sbarisic/MagMouse/hardware/bench/WURTH_ENQUIRY.md

> SUPERSEDED for soldered-wire Rev-A. Historical enquiry record only; no reply
> or additional message is required for this revision. Do not send a follow-up.

# FFC compatibility enquiry

Submitted with the user's authorization through Würth's
[contact form](https://www.we-online.com/en/support/contact) on 2026-09-11.
The site confirmed receipt: "Thank you for your inquiry."
Reply is pending at the user-provided email. Contact details are not stored here.

Requested one 150 mm, 30-conductor, 0.5 mm, same-side-contact FFC for two
Hirose FH12-30S-0.5SH(55) connectors. Requested confirmation of conductor span
14.5 +/-0.05 mm, width 15.5 +/-0.07 mm, end thickness 0.30 +/-0.05 mm,
exposed contacts >=3.5 mm, and stiffener >=0.188 mm. Explained the drawing
tolerance mismatch and inadequate length of trial part 687630050002.

Requested an exact alternative part/drawing, orientation, MOQ, stock, unit
price and delivery options to Croatia 43000, preferably stocked distribution
for one or a few pieces. Explicitly stated that this is an enquiry, not an order.

Do not close cable qualification until the reply or another manufacturer's
conforming drawing identifies an available cable. Measure cable continuity
against the connector pin map before applying power even after qualification.
