sbarisic/MagMouse/hardware/quotes/2026-09-11/Encoder/evidence/drill-report.txt

Drill report for Encoder.kicad_pcb
Created on 2026-09-11T18:30:18

Copper Layer Stackup:
    =============================================================
    L1 :  F.Cu                      front
    L2 :  B.Cu                      back

Drill file 'Encoder-PTH.drl' contains
    plated through holes:
    =============================================================
    T1  0.300mm  0.0118"  (17 holes))

    Total plated holes count 17

Drill file 'Encoder-NPTH.drl' contains
    unplated through holes:
    =============================================================

    Total unplated holes count 0
