sbarisic/MagMouse/hardware/quotes/2026-09-11/Main/evidence/drill-report.txt

Drill report for Main.kicad_pcb
Created on 2026-09-11T18:30:00

Copper Layer Stackup:
    =============================================================
    L1 :  F.Cu                      front
    L2 :  In1.Cu                    in1
    L3 :  In2.Cu                    in2
    L4 :  B.Cu                      back

Drill file 'Main-PTH.drl' contains
    plated through holes:
    =============================================================
    T1  0.200mm  0.0079"  (554 holes))
    T2  0.300mm  0.0118"  (321 holes))
    T3  0.600mm  0.0236"  (4 holes)  (with 4 slots)
    T4  0.700mm  0.0276"  (16 holes))

    Total plated holes count 895

Drill file 'Main-NPTH.drl' contains
    unplated through holes:
    =============================================================
    T1  0.650mm  0.0256"  (2 holes))

    Total unplated holes count 2
