sbarisic/MagMouse/hardware/quotes/2026-09-11/Wheel/evidence/drill-report.txt

Drill report for Wheel.kicad_pcb
Created on 2026-09-11T18:30:11

Copper Layer Stackup:
    =============================================================
    L1 :  F.Cu                      front
    L2 :  In1.Cu                    in1
    L3 :  In2.Cu                    in2
    L4 :  B.Cu                      back

Drill file 'Wheel-PTH.drl' contains
    plated through holes:
    =============================================================
    T1  0.200mm  0.0079"  (56 holes))
    T2  0.300mm  0.0118"  (140 holes))
    T3  1.000mm  0.0394"  (3 holes))

    Total plated holes count 199

Drill file 'Wheel-NPTH.drl' contains
    unplated through holes:
    =============================================================

    Total unplated holes count 0
