sbarisic/MagMouse/hardware/bench/copper-images/index.html

# MagMouse: copper layer review

Click a preview for the full-resolution image (up to 6000 pixels), or open the SVG for unrestricted zoom.

All layers are viewed from the TOP, without mirroring, so positions line up between layers. B.Cu is a through-board view, not an underside photograph. Plots include saved filled zones, tracks, pads, actual drill openings and Edge.Cuts; they exclude solder mask and silkscreen.

Panel note: this is the current working geometry, updated after the JLC submission. The Main-right and Encoder-top replacement tabs now connect across their full width to both board and frame. Images are for manual review, not replacement fabrication files.

Gallery generated 2026-09-13T02:50:26.760Z. Source hashes below identify the board geometry; refresh older open image tabs.

All router corner close-ups

Detail views: U16 pad and via entries · Main B.Cu repair · Wheel MISO simplification · U6 coil via entry · repaired pictured corner · both relocated tabs.

Source identities: SHA-256 manifest. No source board was edited or refilled by this export.

## Main — F.Cu

Source 8409ba354f256351

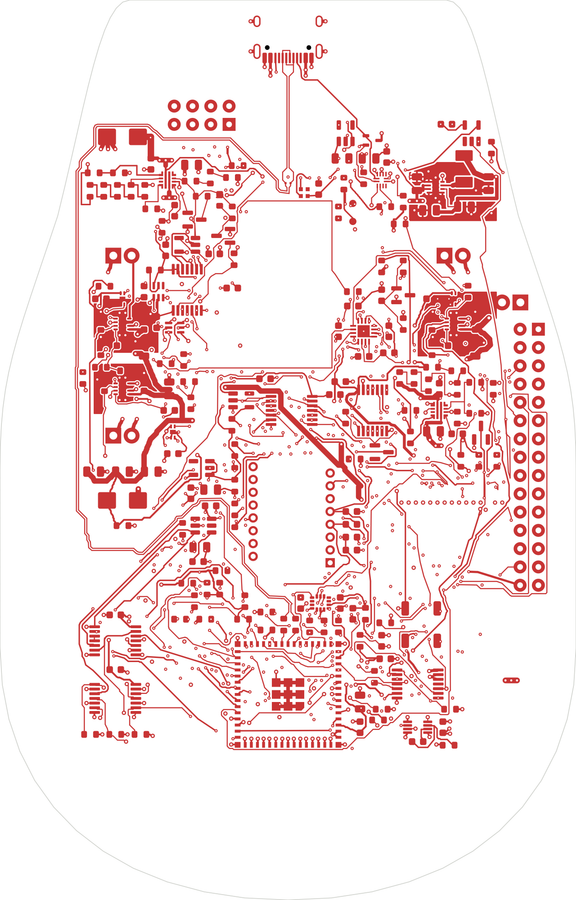
[picture p1: hardware/bench/copper-images/Main-F.Cu-preview.png]
Main F.Cu copper


Full-resolution PNG · Vector SVG

## Main — In1.Cu

Source 8409ba354f256351

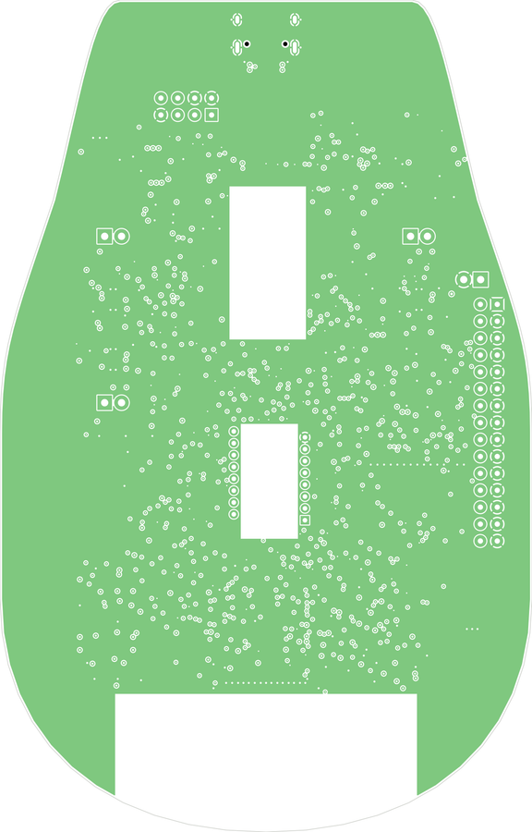
[picture p2: hardware/bench/copper-images/Main-In1.Cu-preview.png]
Main In1.Cu copper


Full-resolution PNG · Vector SVG

## Main — In2.Cu

Source 8409ba354f256351

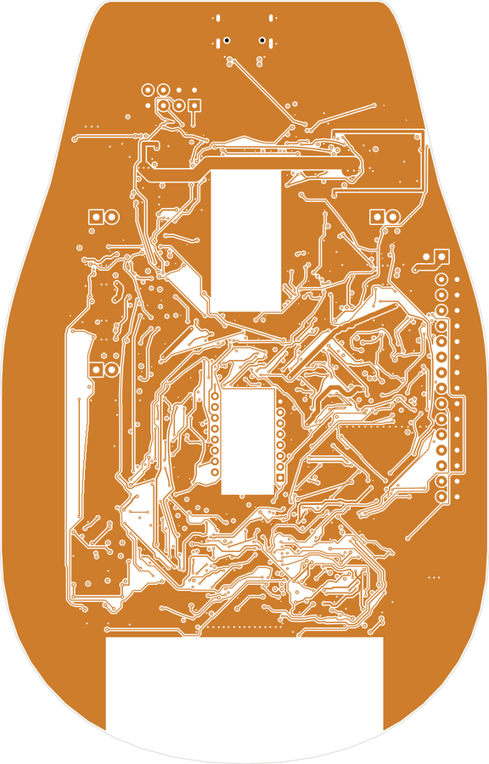
[picture p3: hardware/bench/copper-images/Main-In2.Cu-preview.png]
Main In2.Cu copper


Full-resolution PNG · Vector SVG

## Main — B.Cu

Source 8409ba354f256351

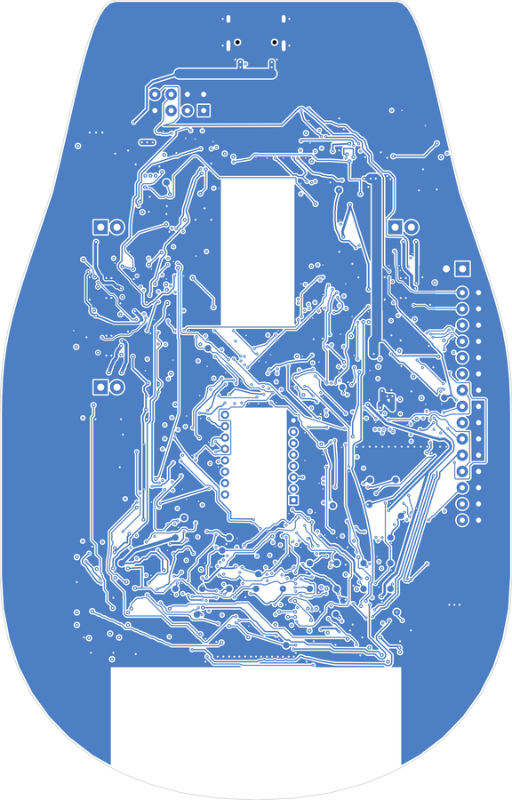
[picture p4: hardware/bench/copper-images/Main-B.Cu-preview.png]
Main B.Cu copper


Full-resolution PNG · Vector SVG

## Wheel — F.Cu

Source e2eaaa13c60e927e

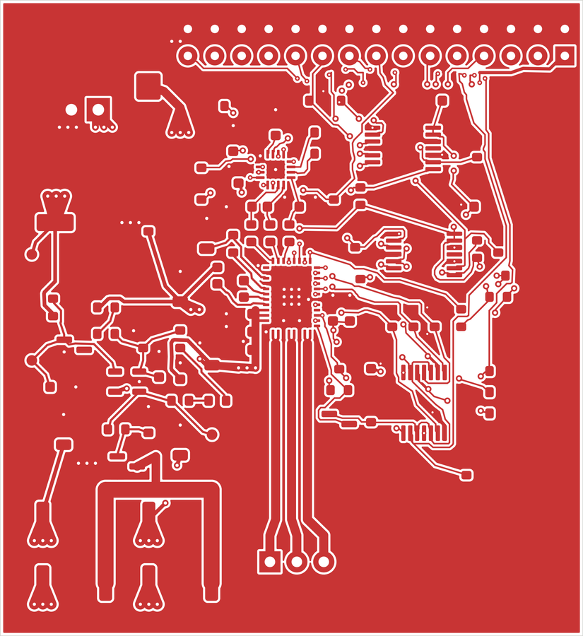
[picture p5: hardware/bench/copper-images/Wheel-F.Cu-preview.png]
Wheel F.Cu copper


Full-resolution PNG · Vector SVG

## Wheel — In1.Cu

Source e2eaaa13c60e927e

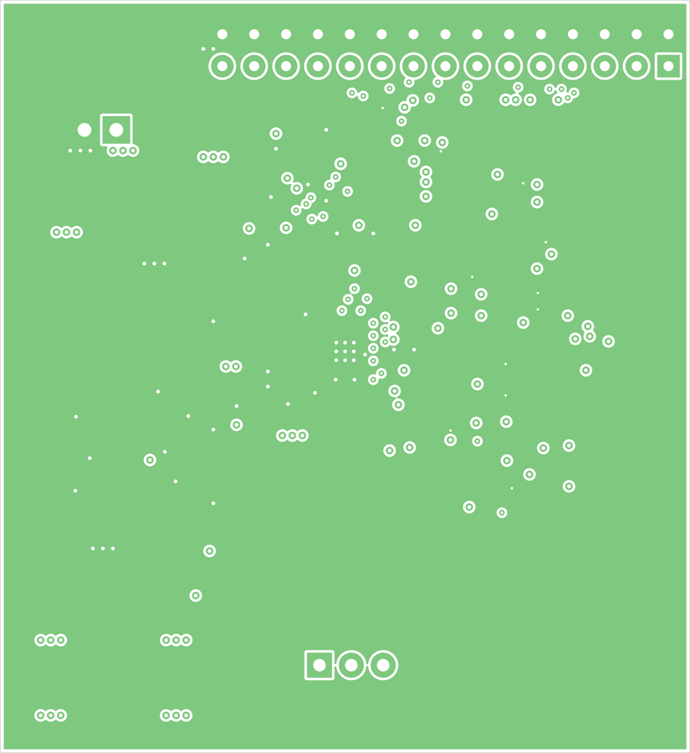
[picture p6: hardware/bench/copper-images/Wheel-In1.Cu-preview.png]
Wheel In1.Cu copper


Full-resolution PNG · Vector SVG

## Wheel — In2.Cu

Source e2eaaa13c60e927e

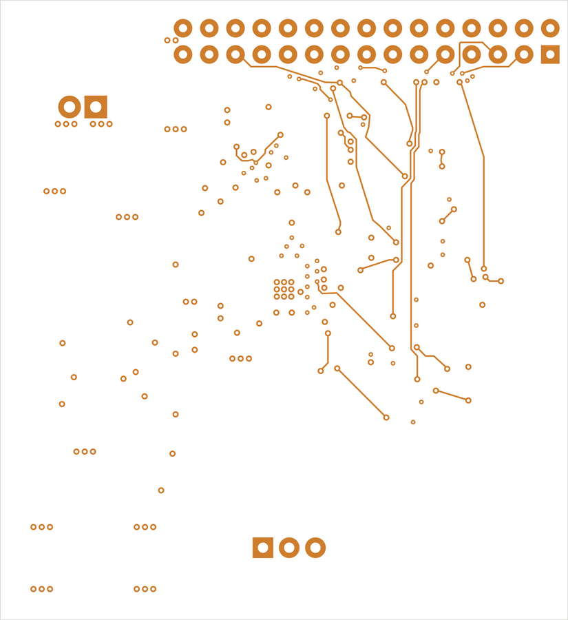
[picture p7: hardware/bench/copper-images/Wheel-In2.Cu-preview.png]
Wheel In2.Cu copper


Full-resolution PNG · Vector SVG

## Wheel — B.Cu

Source e2eaaa13c60e927e

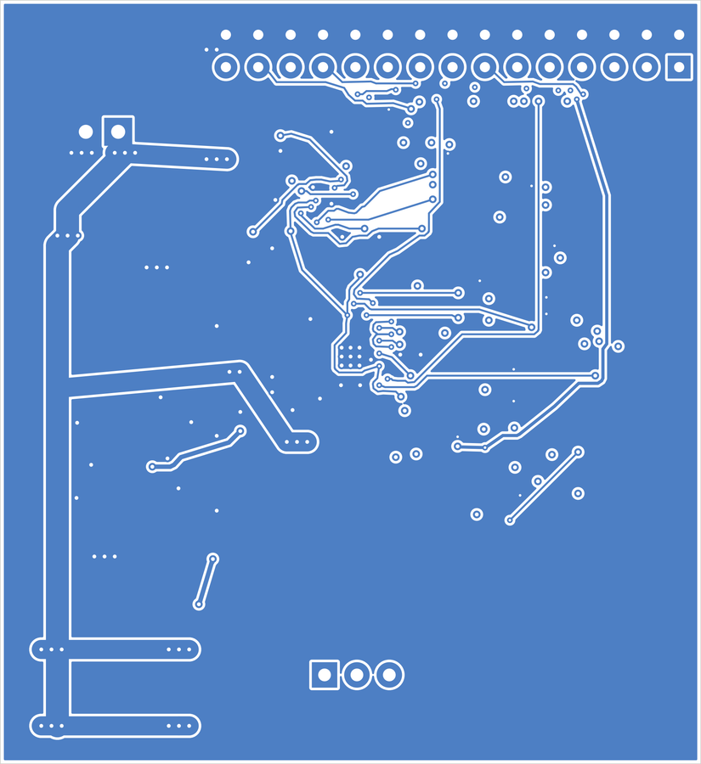
[picture p8: hardware/bench/copper-images/Wheel-B.Cu-preview.png]
Wheel B.Cu copper


Full-resolution PNG · Vector SVG

## Encoder — F.Cu

Source 32b3366d89d79553

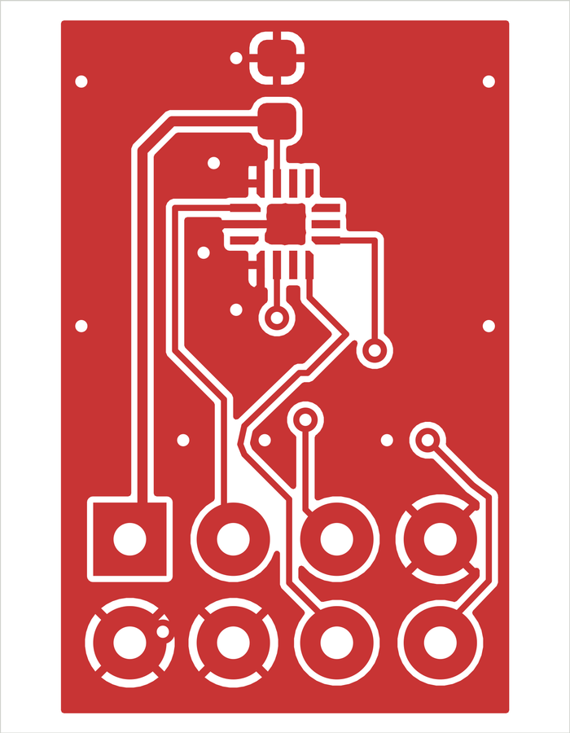
[picture p9: hardware/bench/copper-images/Encoder-F.Cu-preview.png]
Encoder F.Cu copper


Full-resolution PNG · Vector SVG

## Encoder — In1.Cu

Source 32b3366d89d79553

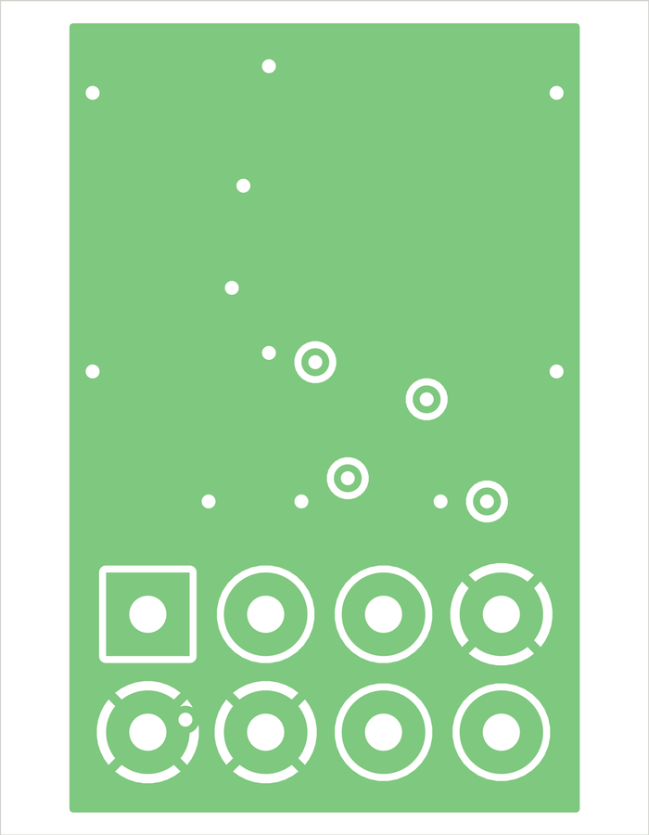
[picture p10: hardware/bench/copper-images/Encoder-In1.Cu-preview.png]
Encoder In1.Cu copper


Full-resolution PNG · Vector SVG

## Encoder — In2.Cu

Source 32b3366d89d79553

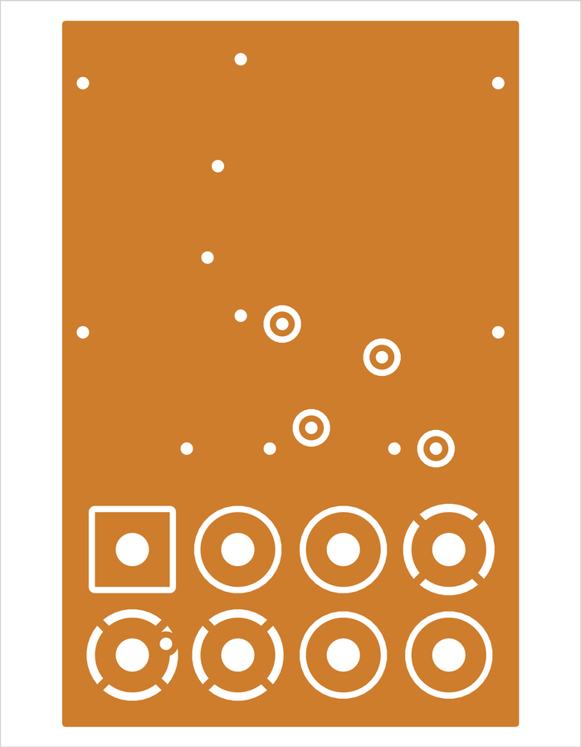
[picture p11: hardware/bench/copper-images/Encoder-In2.Cu-preview.png]
Encoder In2.Cu copper


Full-resolution PNG · Vector SVG

## Encoder — B.Cu

Source 32b3366d89d79553

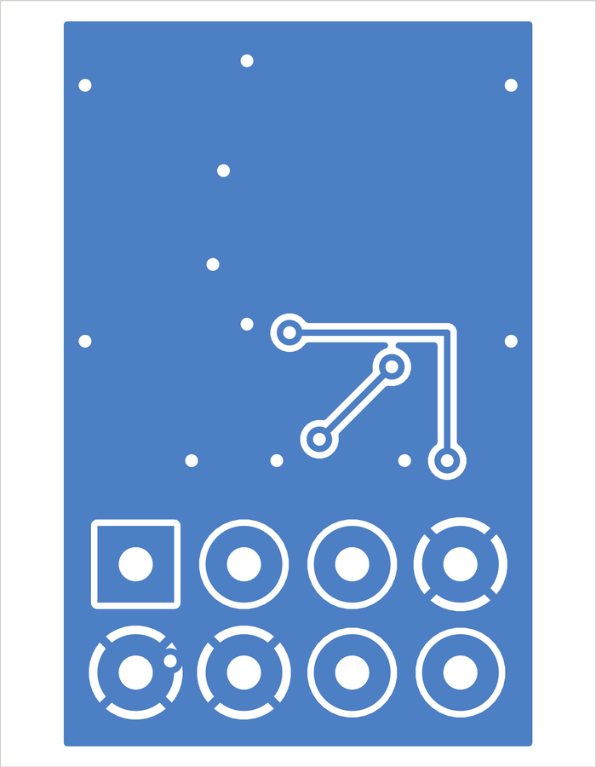
[picture p12: hardware/bench/copper-images/Encoder-B.Cu-preview.png]
Encoder B.Cu copper


Full-resolution PNG · Vector SVG

## Panel — F.Cu

Source 6ce26abbf629e559

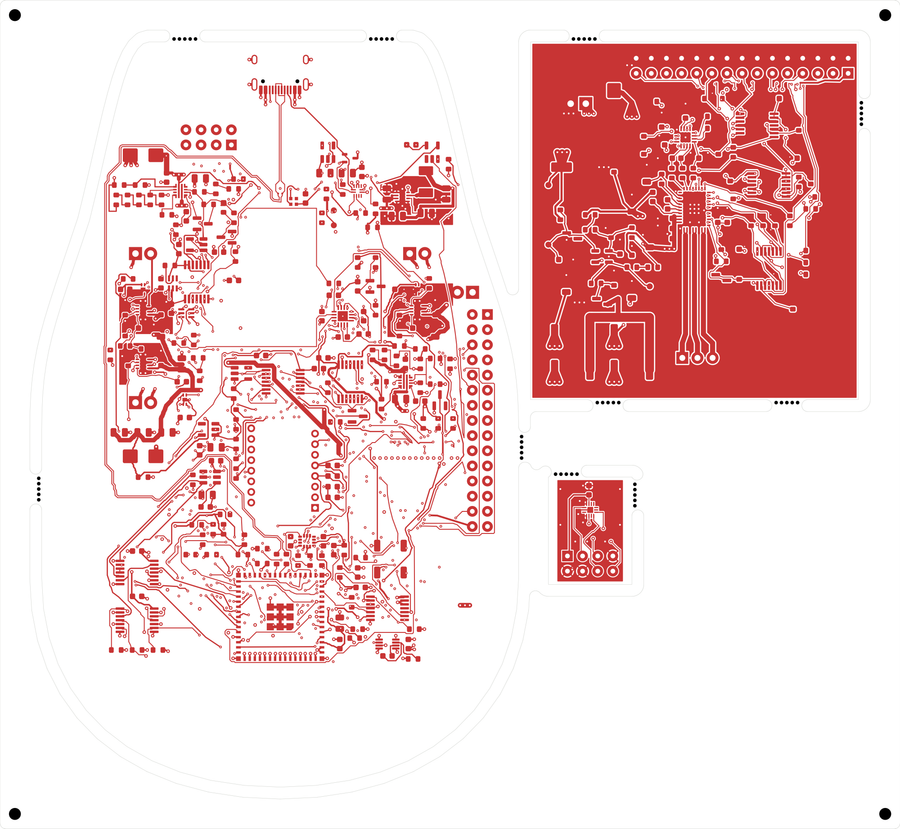
[picture p13: hardware/bench/copper-images/Panel-F.Cu-preview.png]
Panel F.Cu copper


Full-resolution PNG · Vector SVG

## Panel — In1.Cu

Source 6ce26abbf629e559

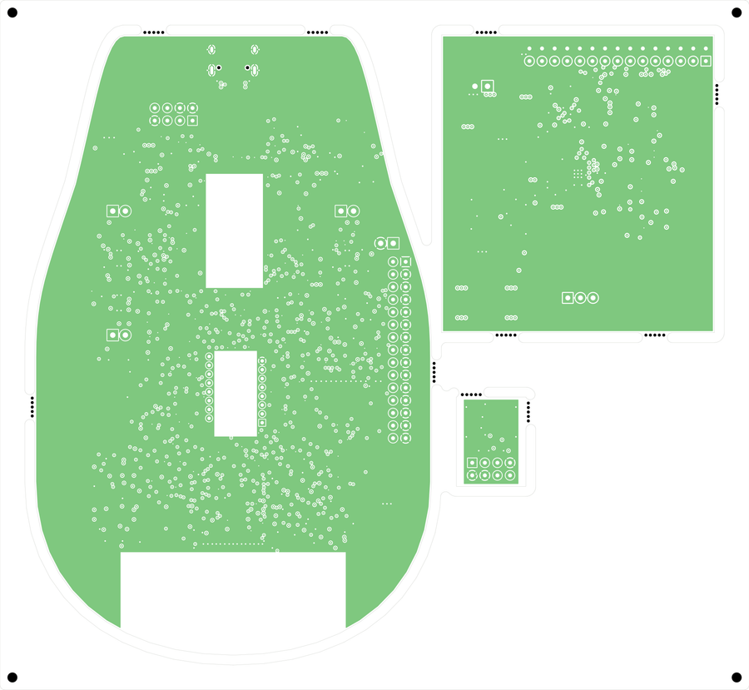
[picture p14: hardware/bench/copper-images/Panel-In1.Cu-preview.png]
Panel In1.Cu copper


Full-resolution PNG · Vector SVG

## Panel — In2.Cu

Source 6ce26abbf629e559

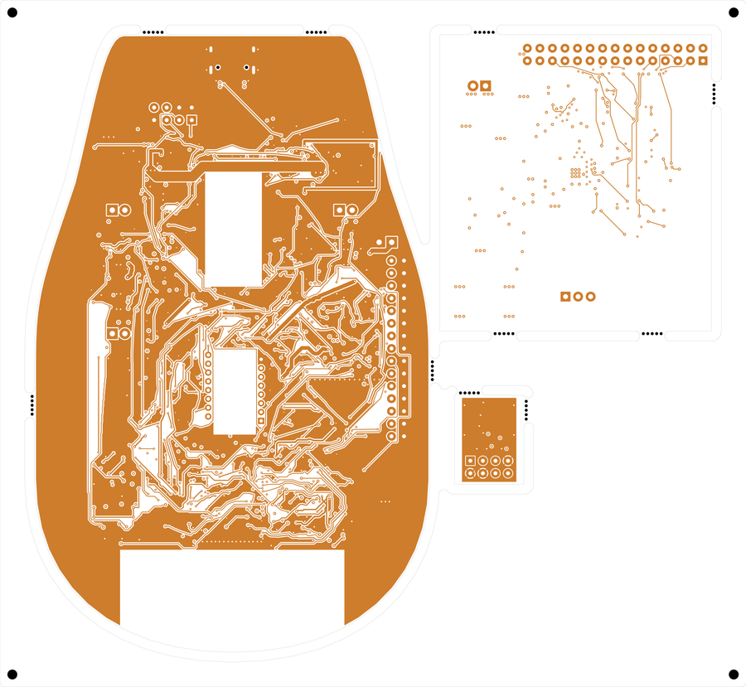
[picture p15: hardware/bench/copper-images/Panel-In2.Cu-preview.png]
Panel In2.Cu copper


Full-resolution PNG · Vector SVG

## Panel — B.Cu

Source 6ce26abbf629e559

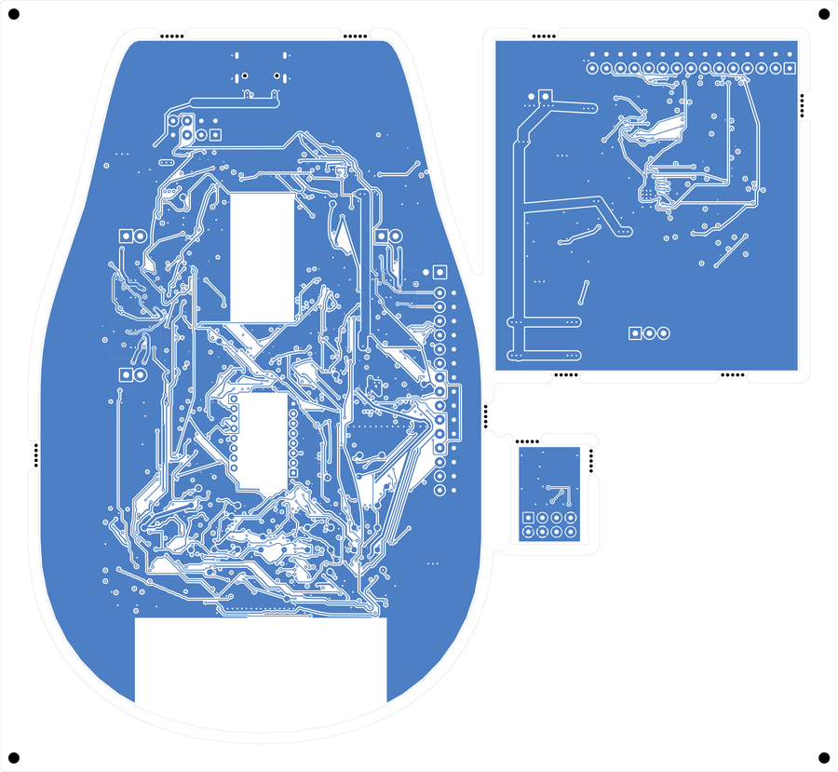
[picture p16: hardware/bench/copper-images/Panel-B.Cu-preview.png]
Panel B.Cu copper


Full-resolution PNG · Vector SVG
