sbarisic/MagMouse/hardware/bench/router-images/index.html

# 2 mm cutter / 1 mm radius

Panel SHA256: 6ce26abbf629e5592f26f47651ea0b0219b7810e1122b6fbaca9ea3bea7f399e

All 40 retained corner patches; 4 × 4 mm views. Pale green is retained material; white is routed away. Factory CAM approval remains pending.

## corner-01, opening 1

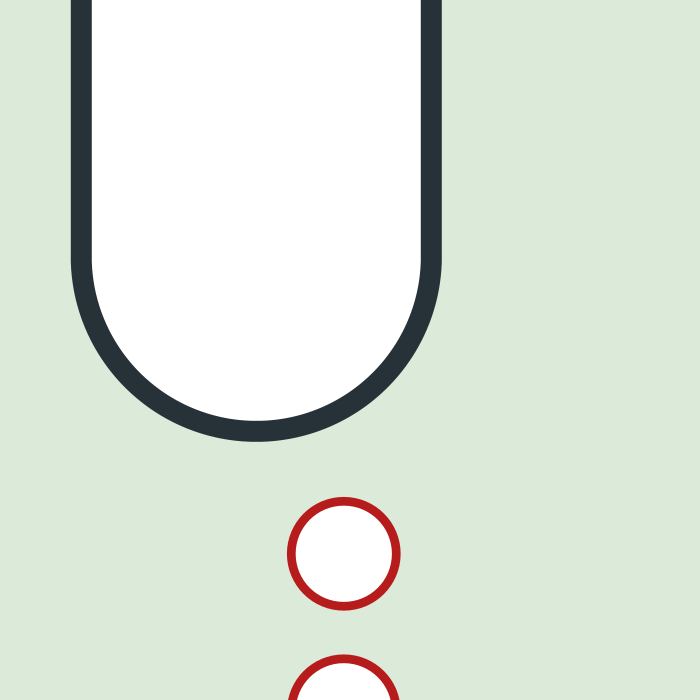
[picture p17: hardware/bench/router-images/corner-01.png]


## corner-02, opening 1

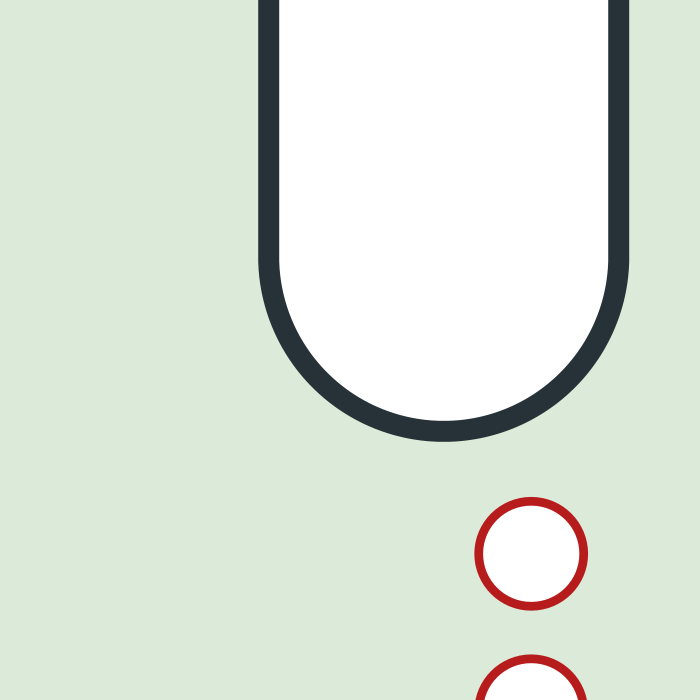
[picture p18: hardware/bench/router-images/corner-02.png]


## corner-03, opening 1

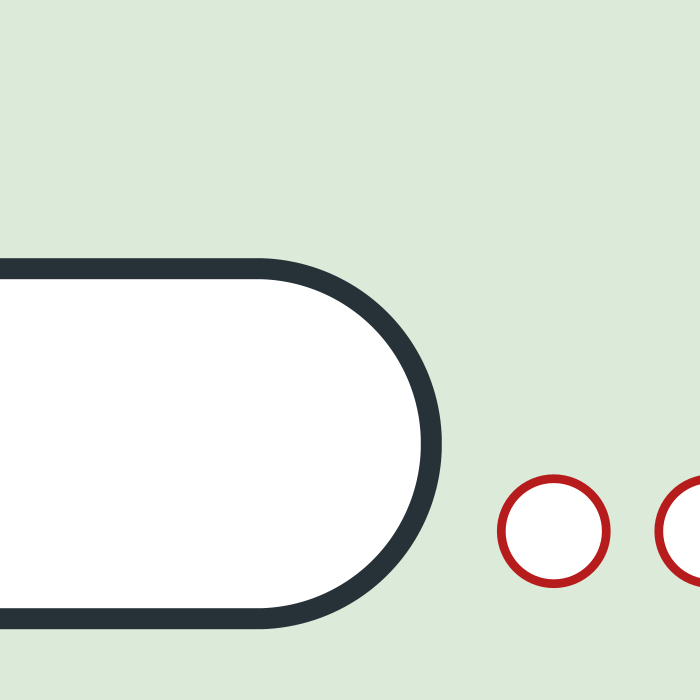
[picture p19: hardware/bench/router-images/corner-03.png]


## corner-04, opening 1

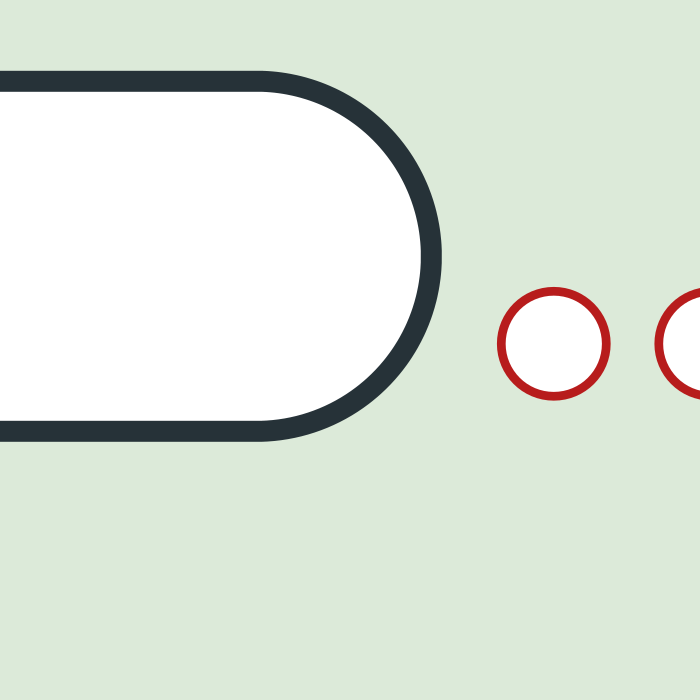
[picture p20: hardware/bench/router-images/corner-04.png]


## corner-05, opening 2

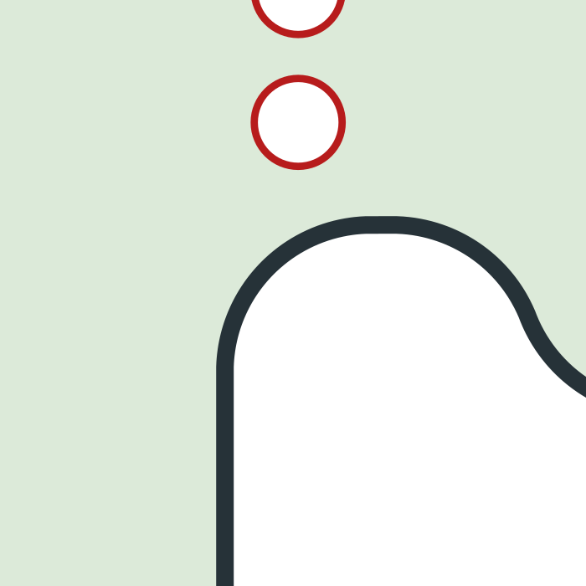
[picture p21: hardware/bench/router-images/corner-05.png]


## corner-06, opening 2

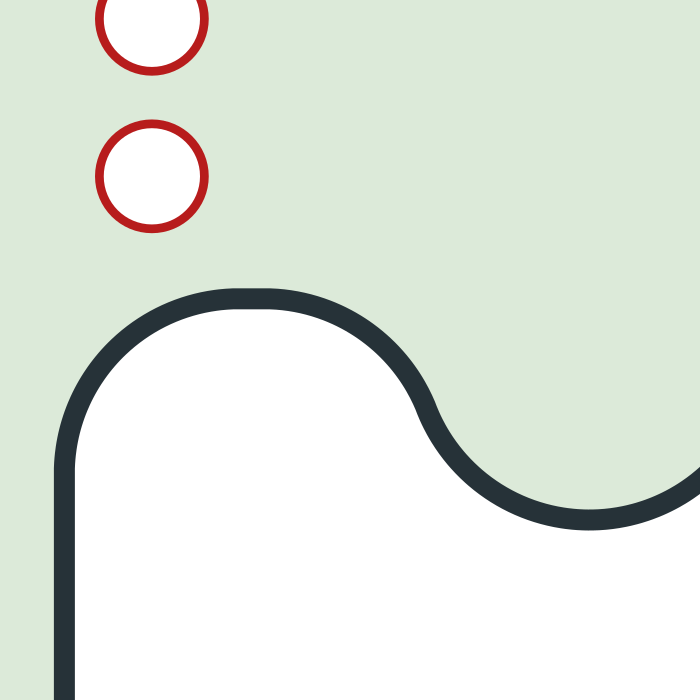
[picture p22: hardware/bench/router-images/corner-06.png]


## corner-07, opening 2

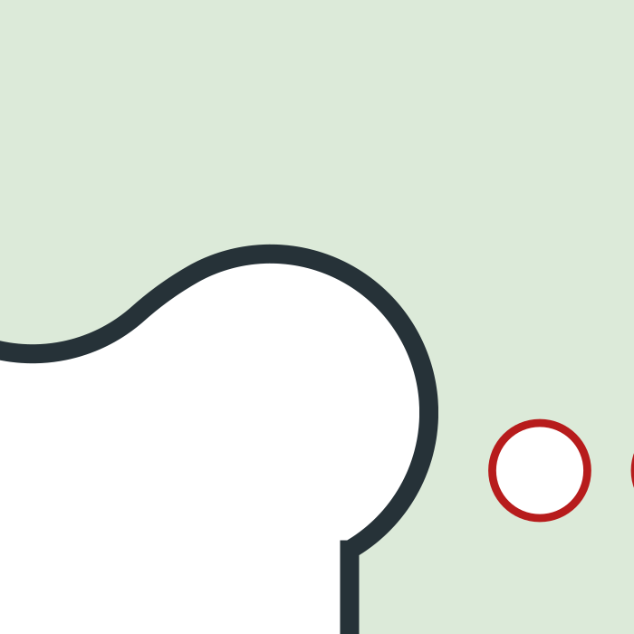
[picture p23: hardware/bench/router-images/corner-07.png]


## corner-08, opening 2

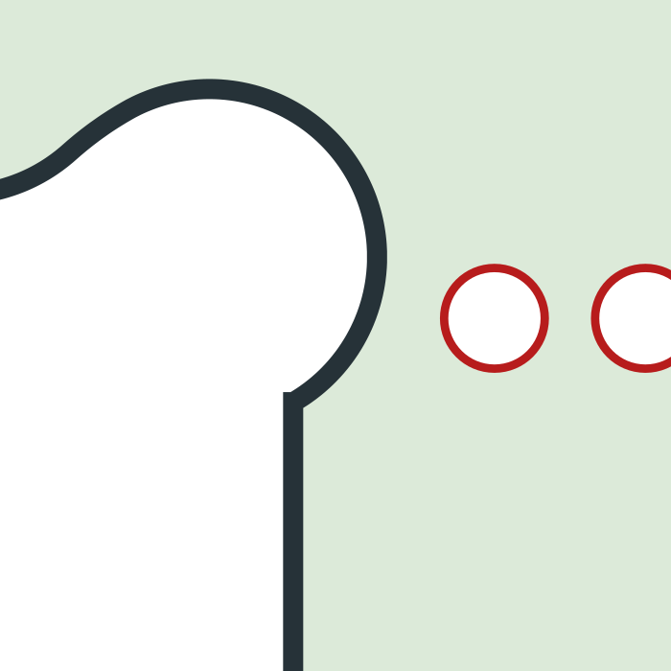
[picture p24: hardware/bench/router-images/corner-08.png]


## corner-09, opening 2

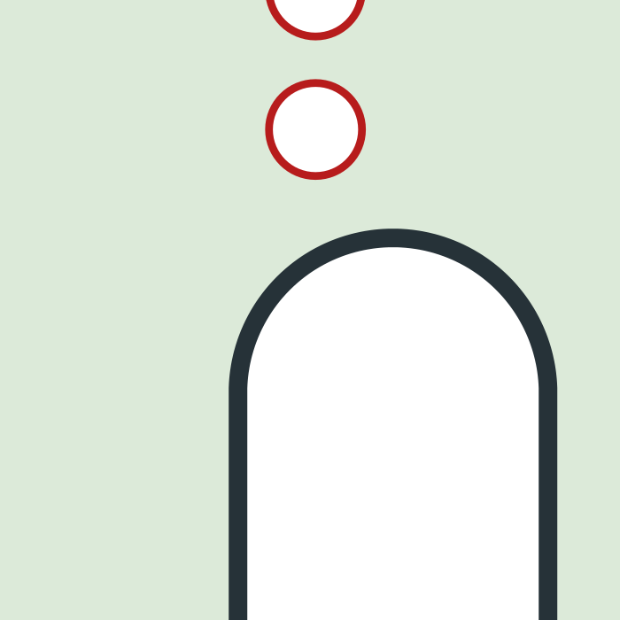
[picture p25: hardware/bench/router-images/corner-09.png]


## corner-10, opening 2

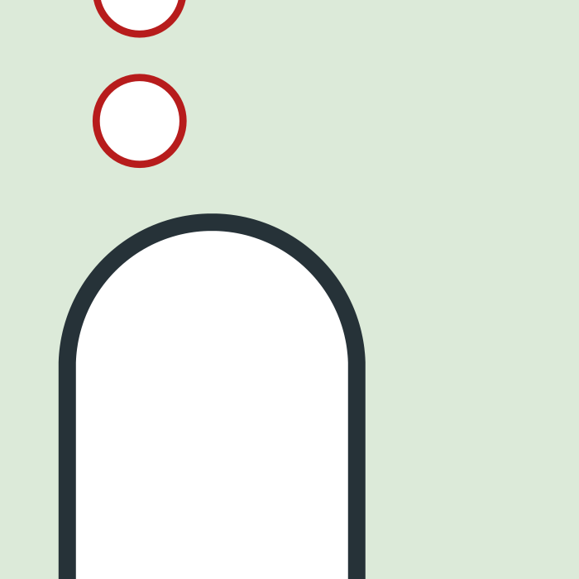
[picture p26: hardware/bench/router-images/corner-10.png]


## corner-11, opening 2

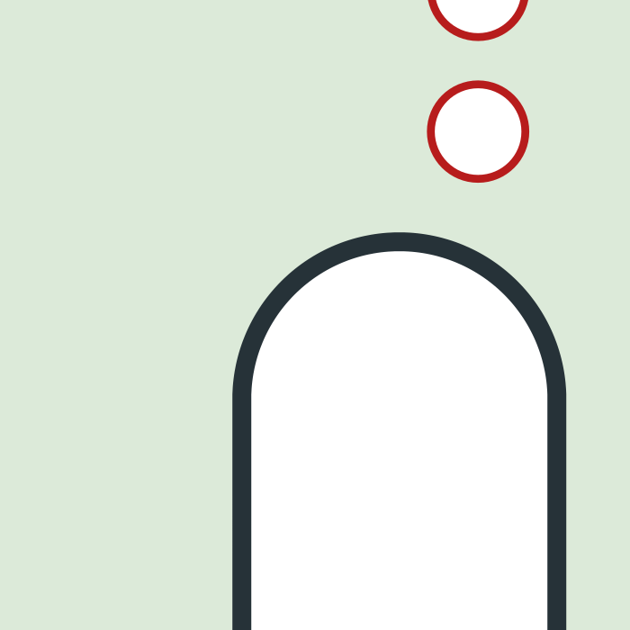
[picture p27: hardware/bench/router-images/corner-11.png]


## corner-12, opening 2

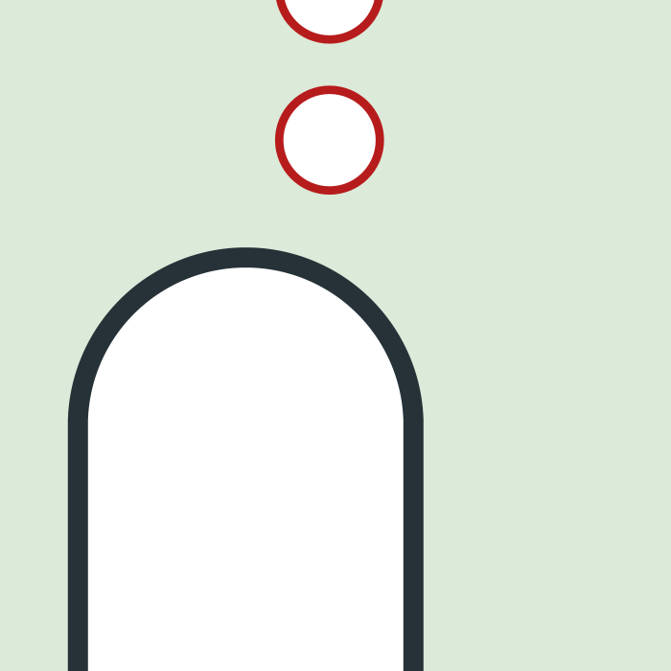
[picture p28: hardware/bench/router-images/corner-12.png]


## corner-13, opening 3

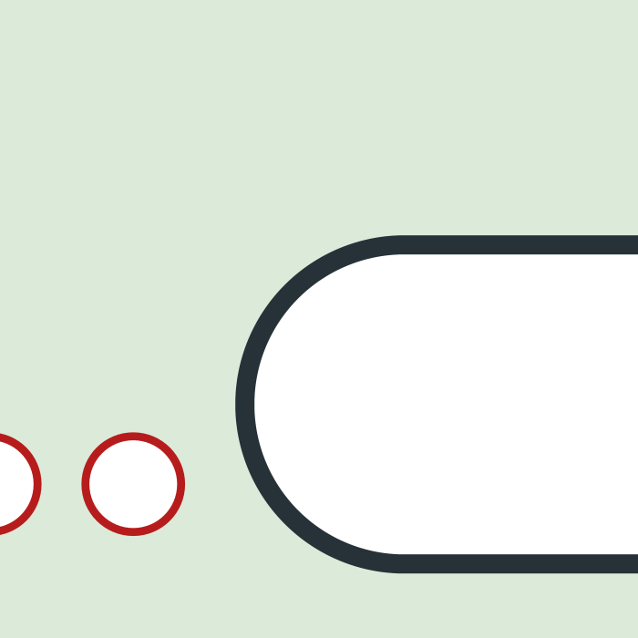
[picture p29: hardware/bench/router-images/corner-13.png]


## corner-14, opening 3

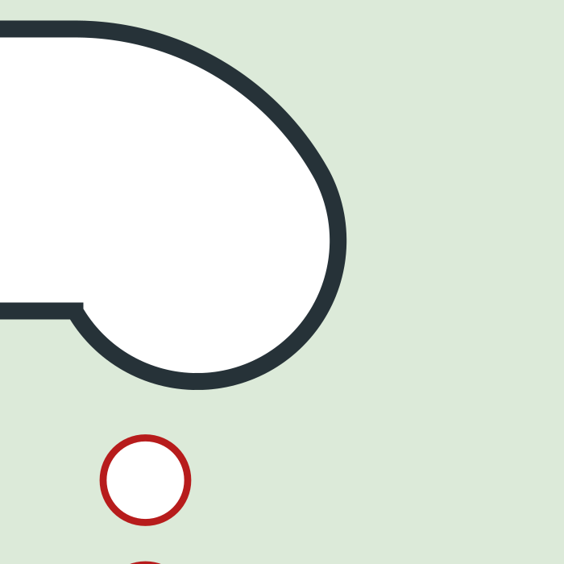
[picture p30: hardware/bench/router-images/corner-14.png]


## corner-15, opening 3

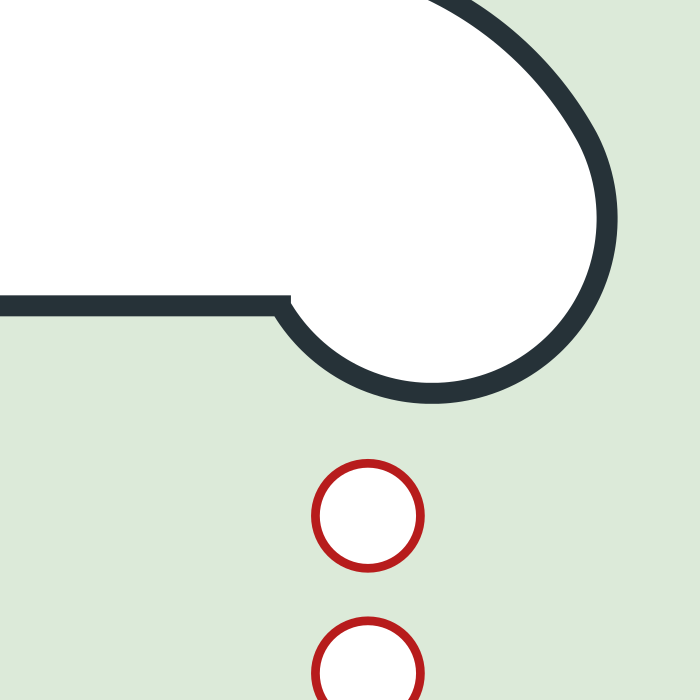
[picture p31: hardware/bench/router-images/corner-15.png]


## corner-16, opening 3

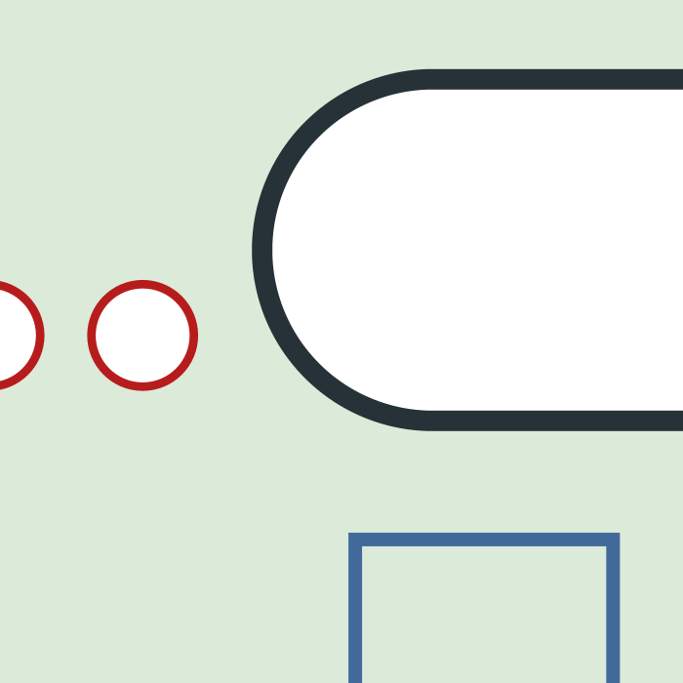
[picture p32: hardware/bench/router-images/corner-16.png]


## corner-17, opening 4

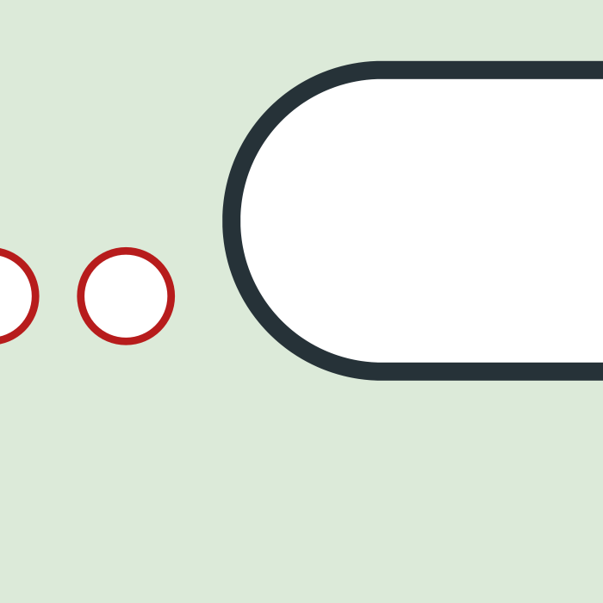
[picture p33: hardware/bench/router-images/corner-17.png]


## corner-18, opening 4

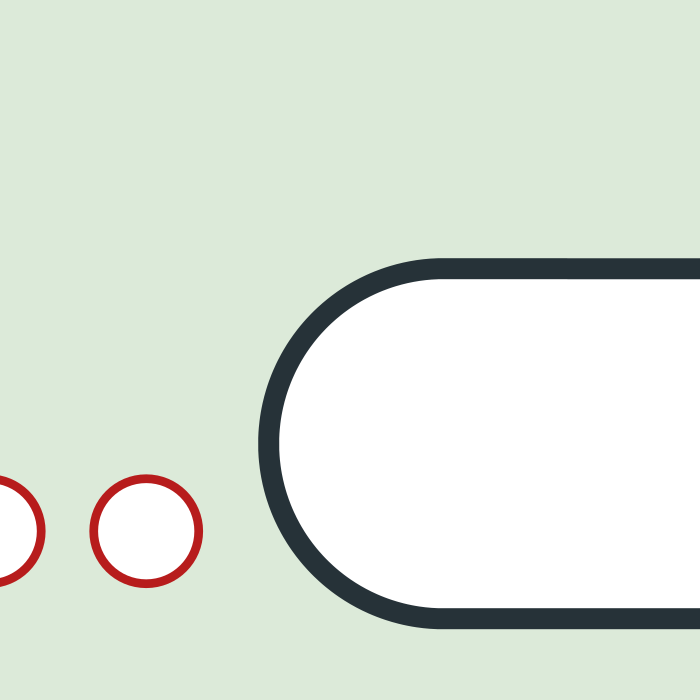
[picture p34: hardware/bench/router-images/corner-18.png]


## corner-19, opening 4

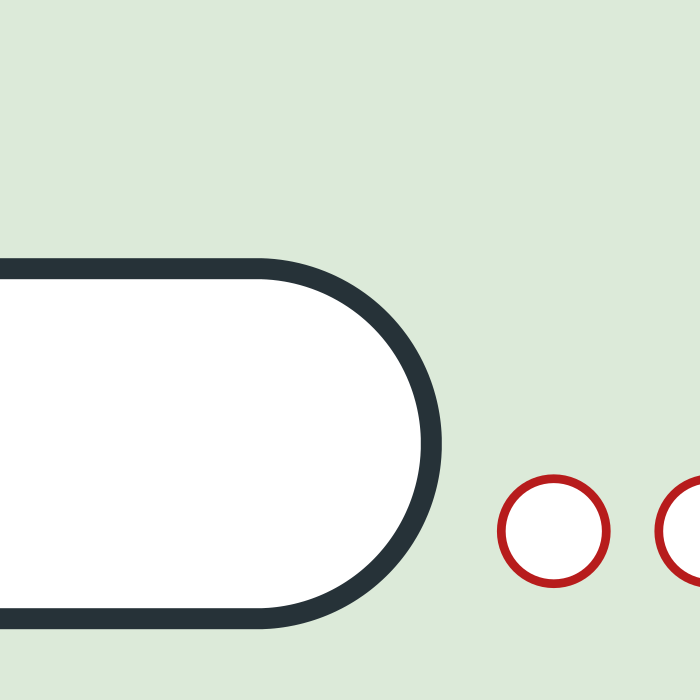
[picture p35: hardware/bench/router-images/corner-19.png]


## corner-20, opening 4

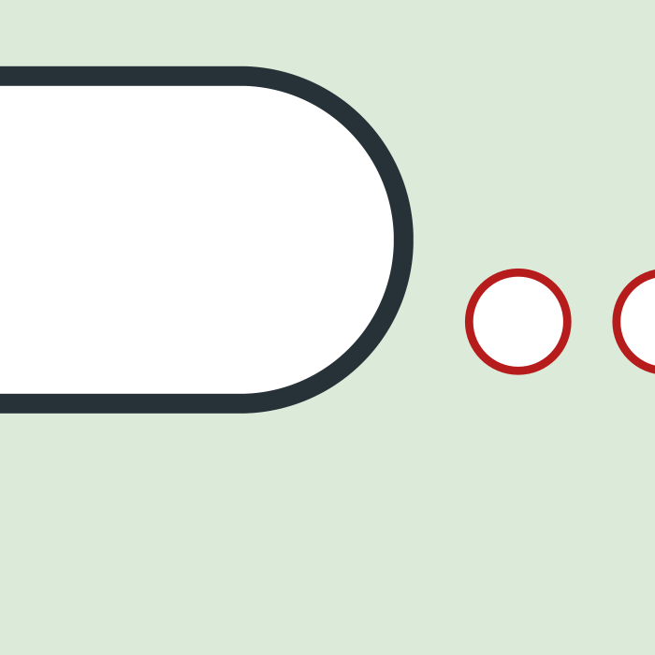
[picture p36: hardware/bench/router-images/corner-20.png]


## corner-21, opening 4

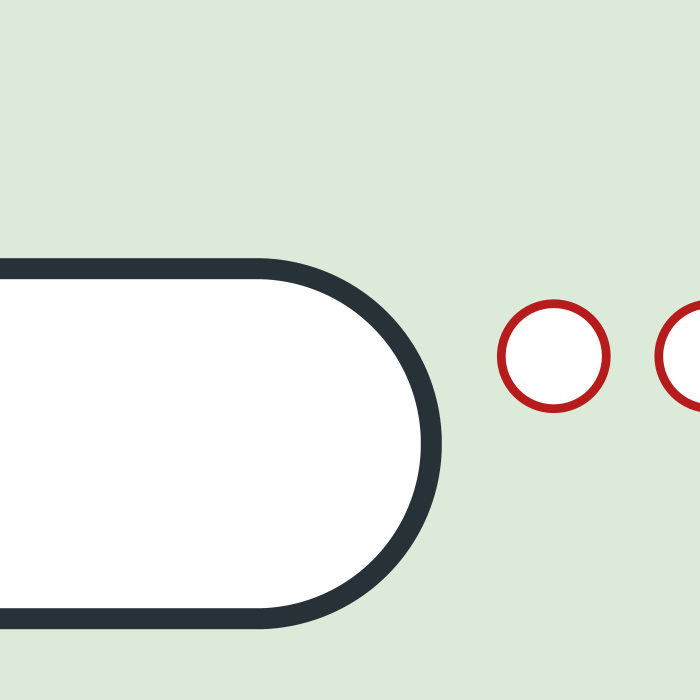
[picture p37: hardware/bench/router-images/corner-21.png]


## corner-22, opening 4

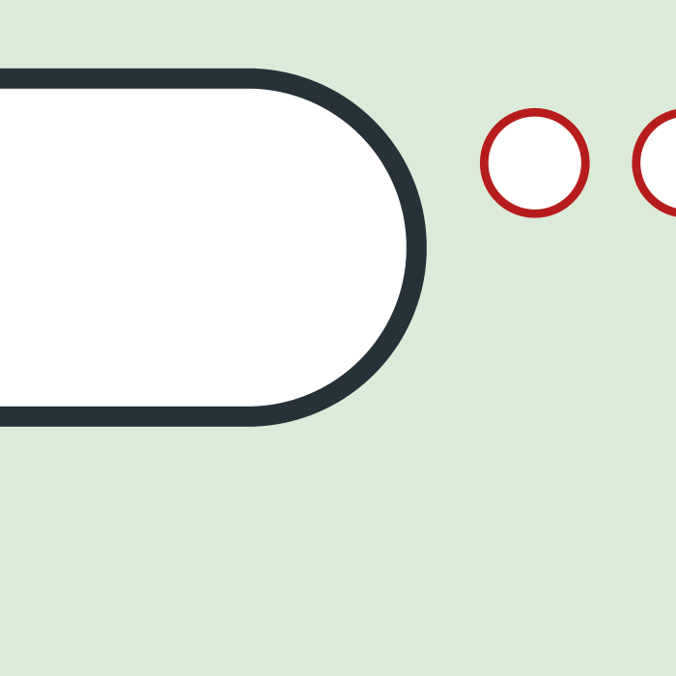
[picture p38: hardware/bench/router-images/corner-22.png]


## corner-23, opening 4

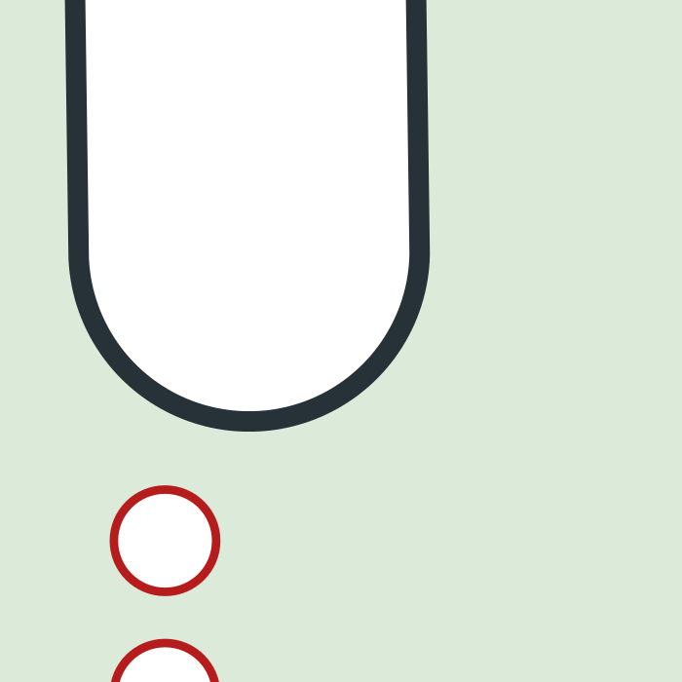
[picture p39: hardware/bench/router-images/corner-23.png]


## corner-24, opening 4

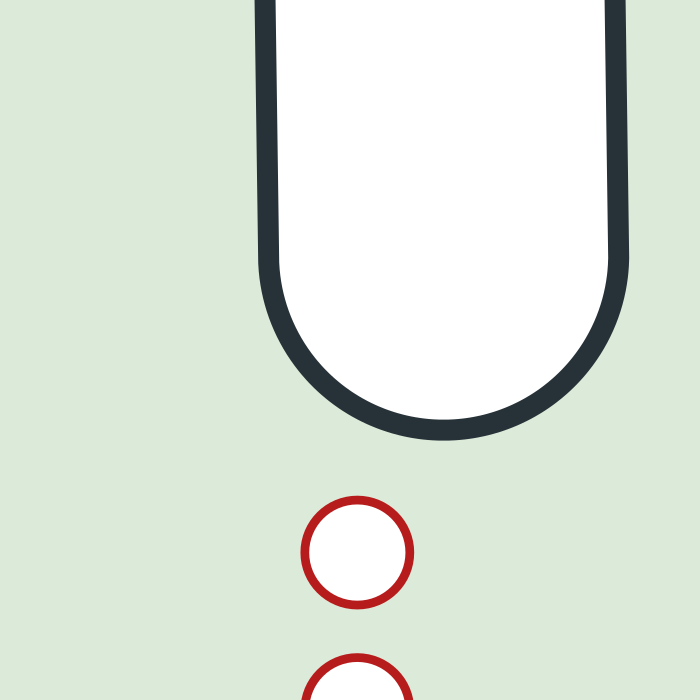
[picture p40: hardware/bench/router-images/corner-24.png]


## corner-25, opening 5

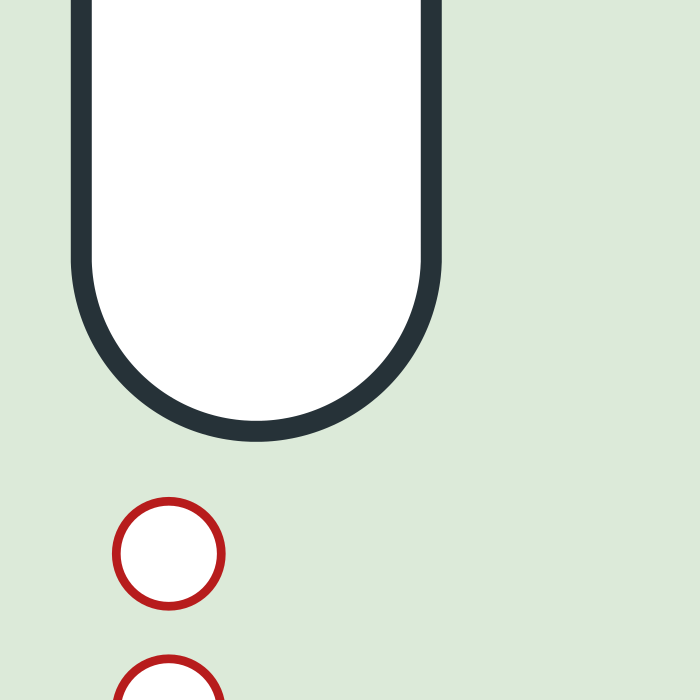
[picture p41: hardware/bench/router-images/corner-25.png]


## corner-26, opening 5

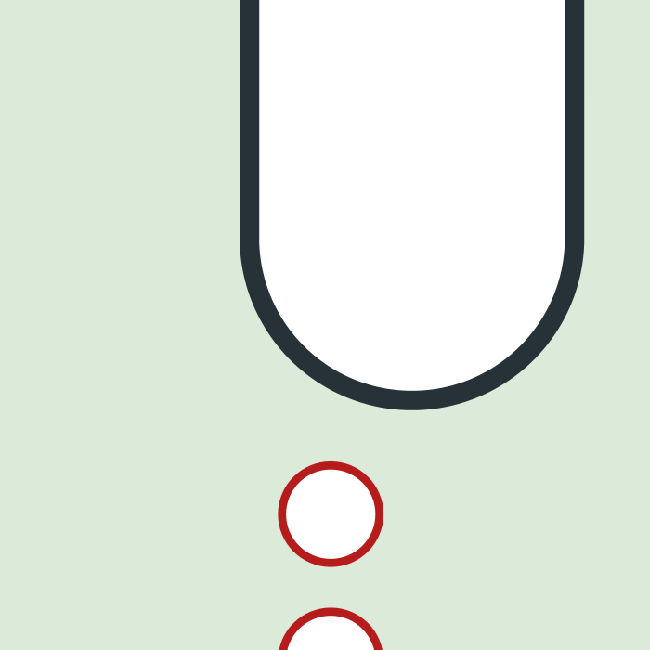
[picture p42: hardware/bench/router-images/corner-26.png]


## corner-27, opening 5

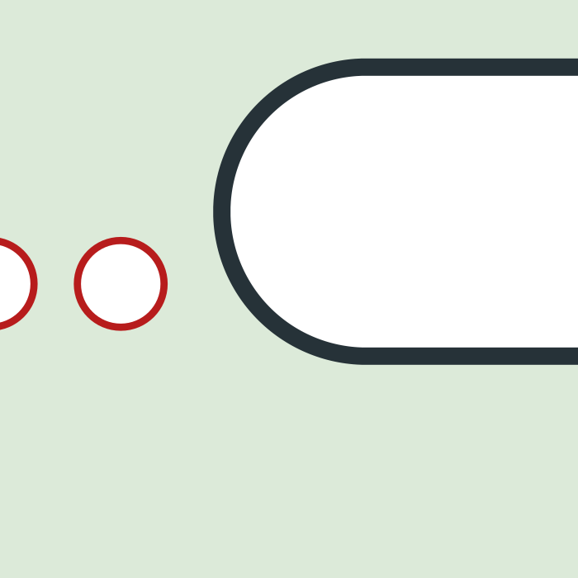
[picture p43: hardware/bench/router-images/corner-27.png]


## corner-28, opening 5

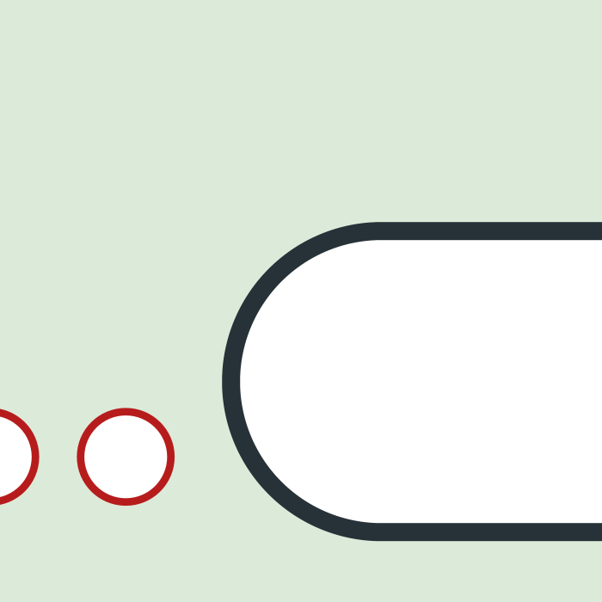
[picture p44: hardware/bench/router-images/corner-28.png]


## corner-29, opening 6

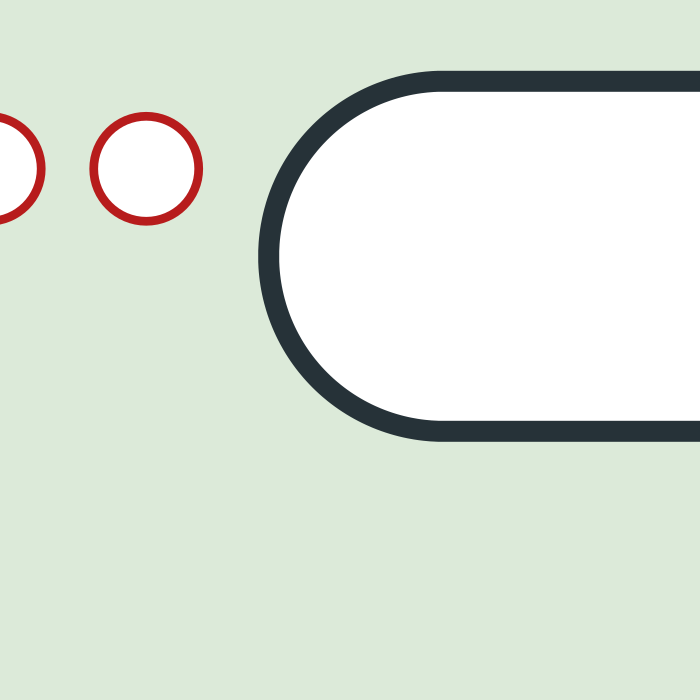
[picture p45: hardware/bench/router-images/corner-29.png]


## corner-30, opening 6

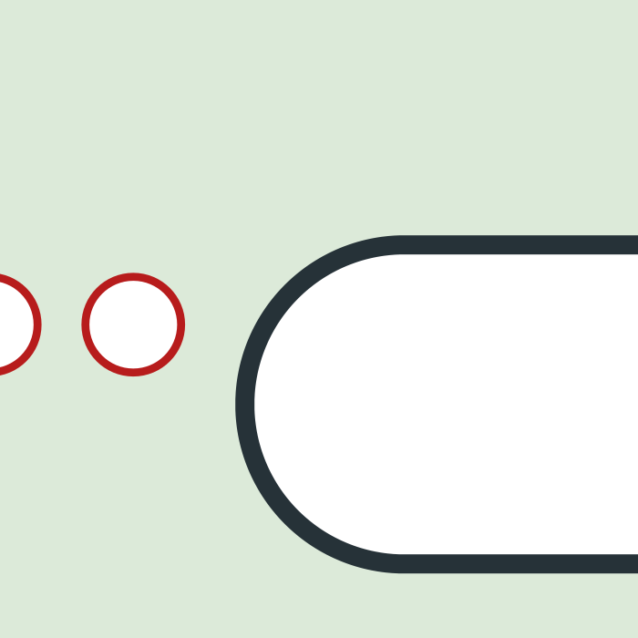
[picture p46: hardware/bench/router-images/corner-30.png]


## corner-31, opening 6

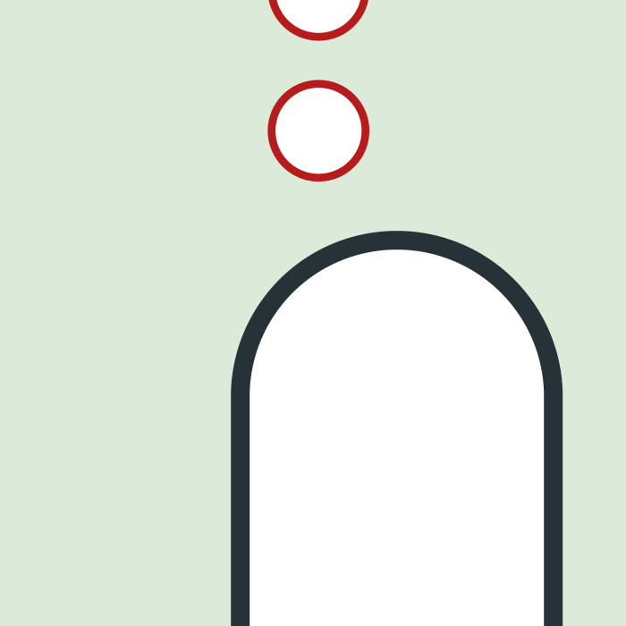
[picture p47: hardware/bench/router-images/corner-31.png]


## corner-32, opening 6

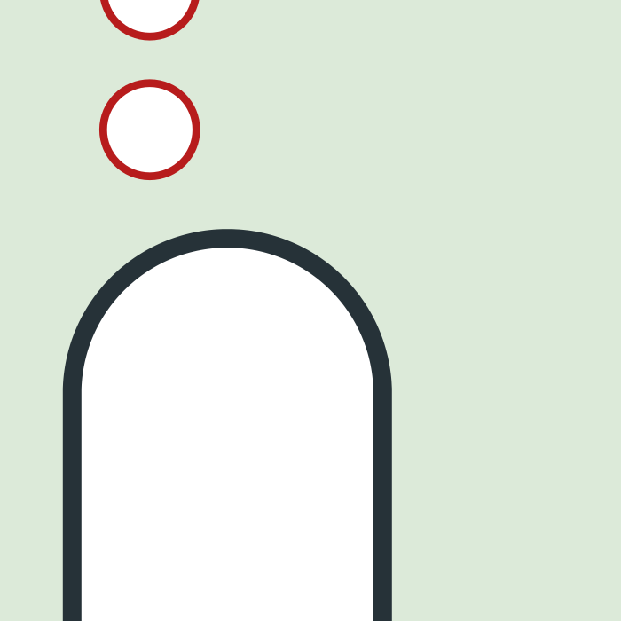
[picture p48: hardware/bench/router-images/corner-32.png]


## corner-33, opening 7

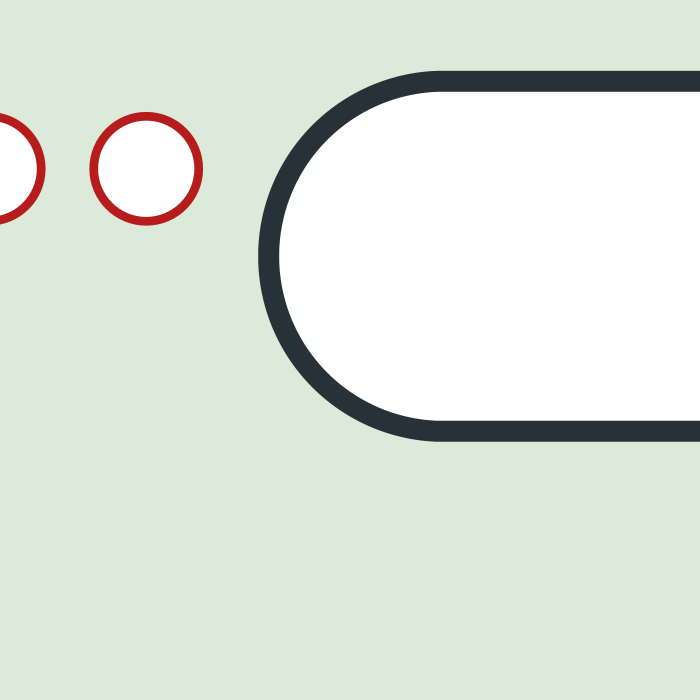
[picture p49: hardware/bench/router-images/corner-33.png]


## corner-34, opening 7

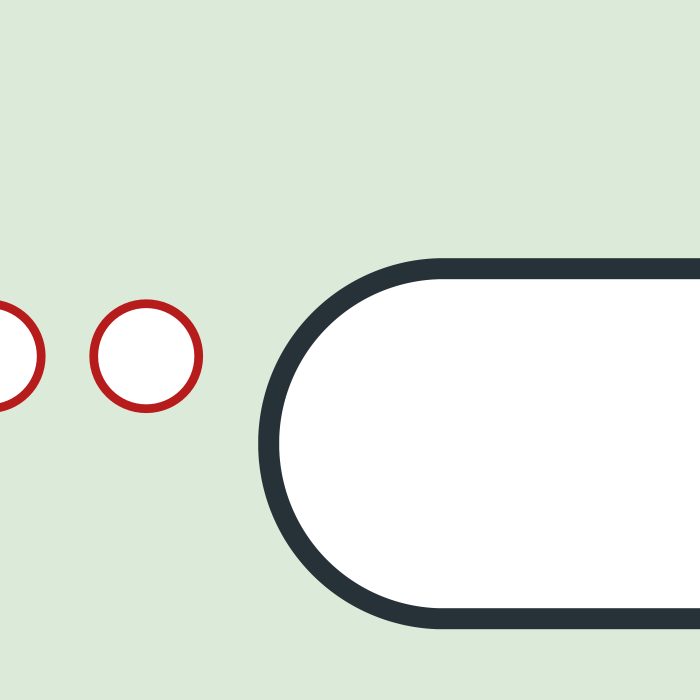
[picture p50: hardware/bench/router-images/corner-34.png]


## corner-35, opening 7

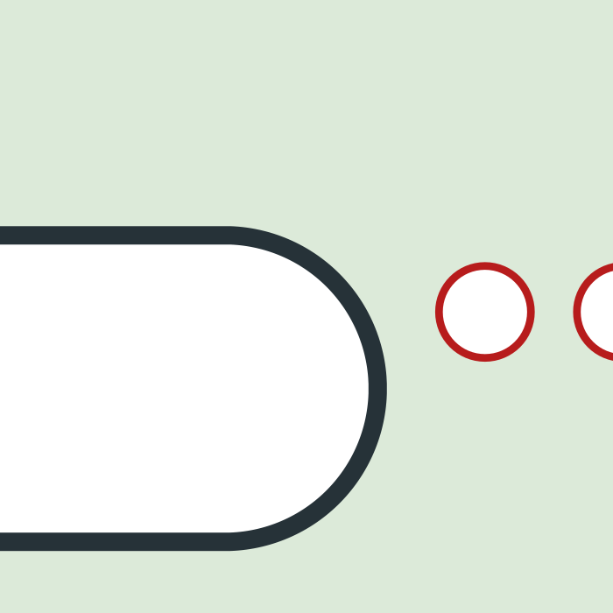
[picture p51: hardware/bench/router-images/corner-35.png]


## corner-36, opening 7

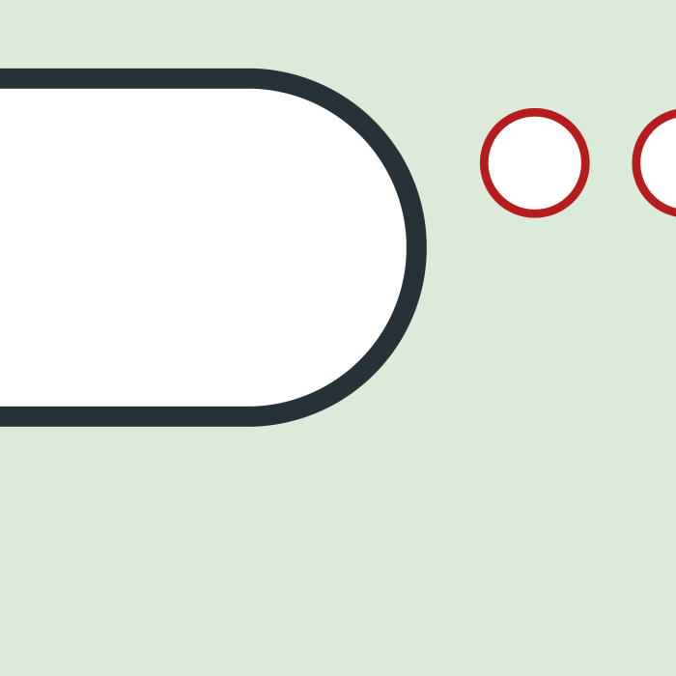
[picture p52: hardware/bench/router-images/corner-36.png]


## corner-37, opening 8

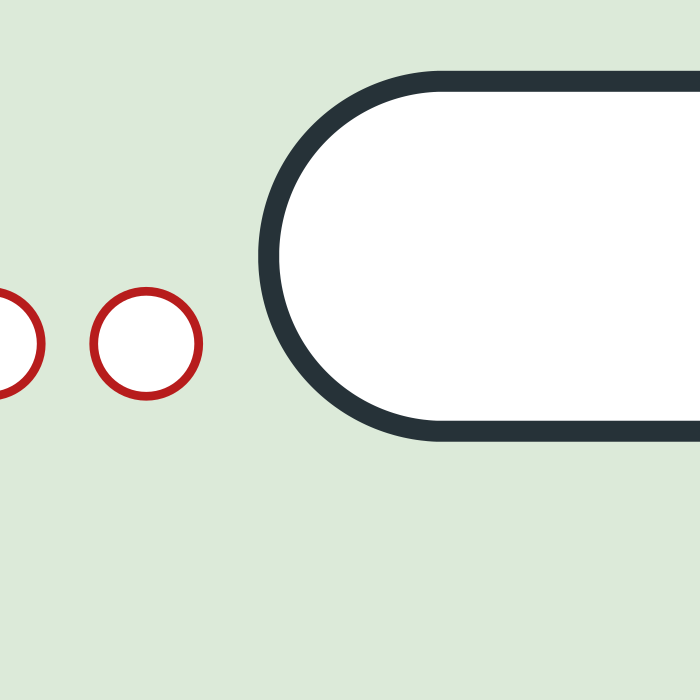
[picture p53: hardware/bench/router-images/corner-37.png]


## corner-38, opening 8

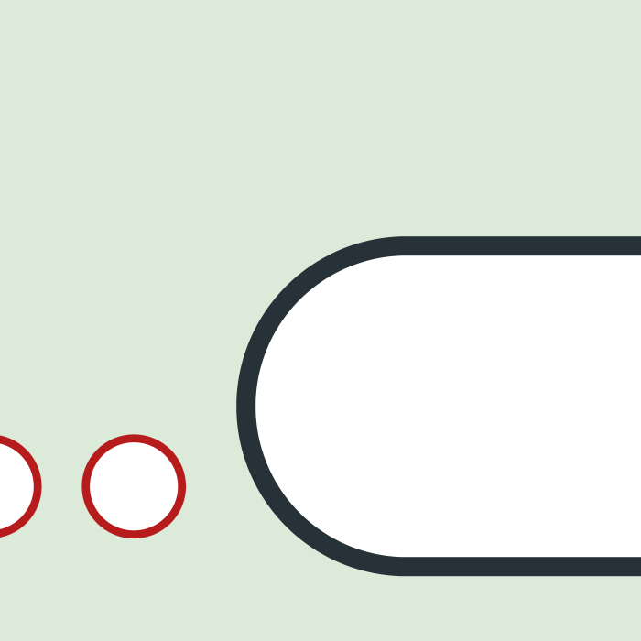
[picture p54: hardware/bench/router-images/corner-38.png]


## corner-39, opening 8

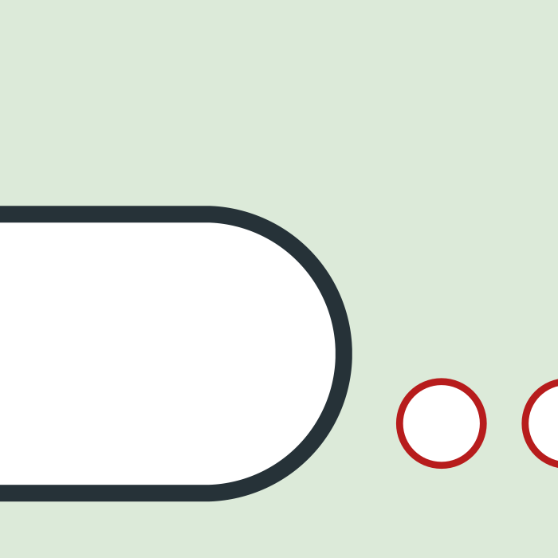
[picture p55: hardware/bench/router-images/corner-39.png]


## corner-40, opening 8

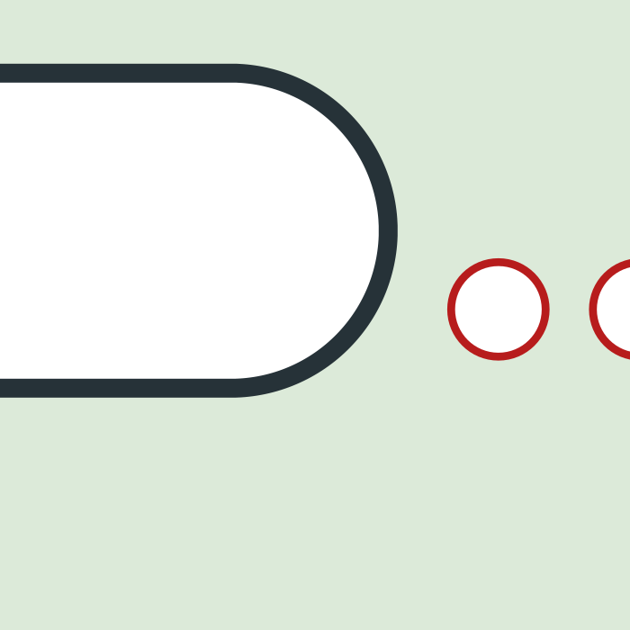
[picture p56: hardware/bench/router-images/corner-40.png]
