sbarisic/MagMouse/hardware/bench/copper-images/Main-encoder-MOSI.png

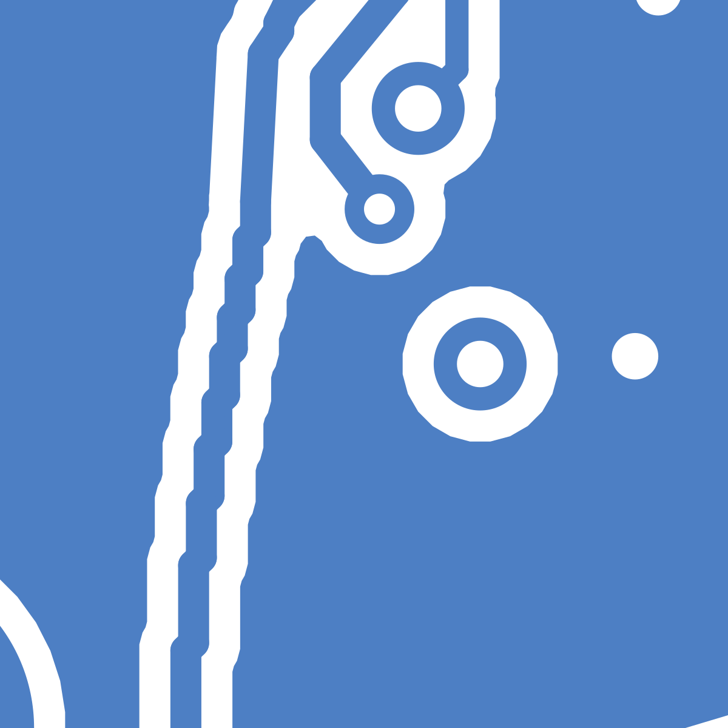
hardware/bench/copper-images/Main-encoder-MOSI.png
