sbarisic/MagMouse/hardware/bench/copper-images/Main-pictured-corner.png

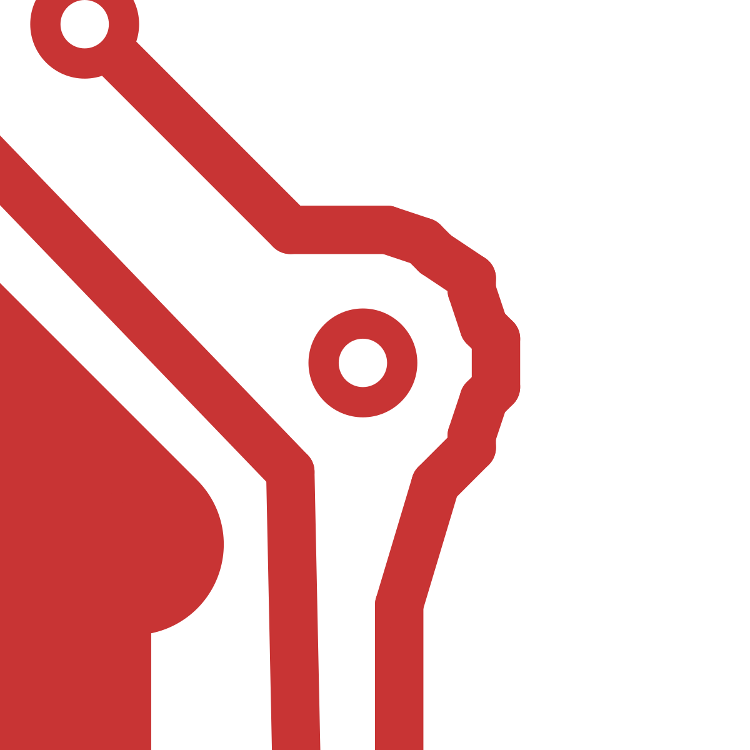
hardware/bench/copper-images/Main-pictured-corner.png
