sbarisic/MagMouse/hardware/bench/copper-images/Main-U6-coil-via.png

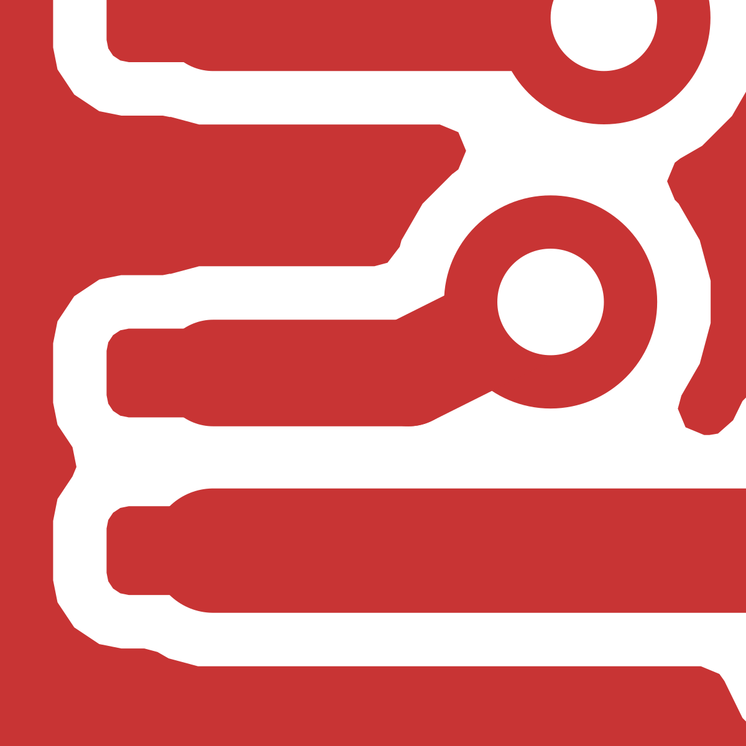
hardware/bench/copper-images/Main-U6-coil-via.png
