sbarisic/MagMouse/hardware/bench/copper-images/Main-U16-pad-via.png

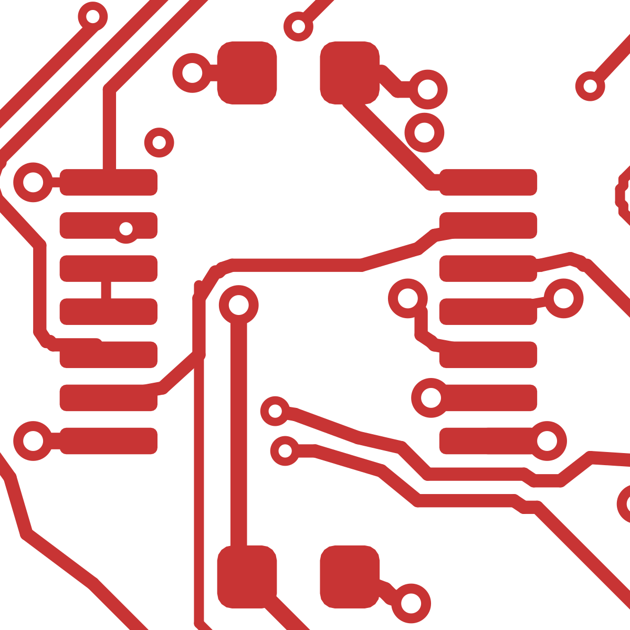
hardware/bench/copper-images/Main-U16-pad-via.png
