sbarisic/MagMouse/hardware/bench/copper-images/Panel-relocated-tabs.png

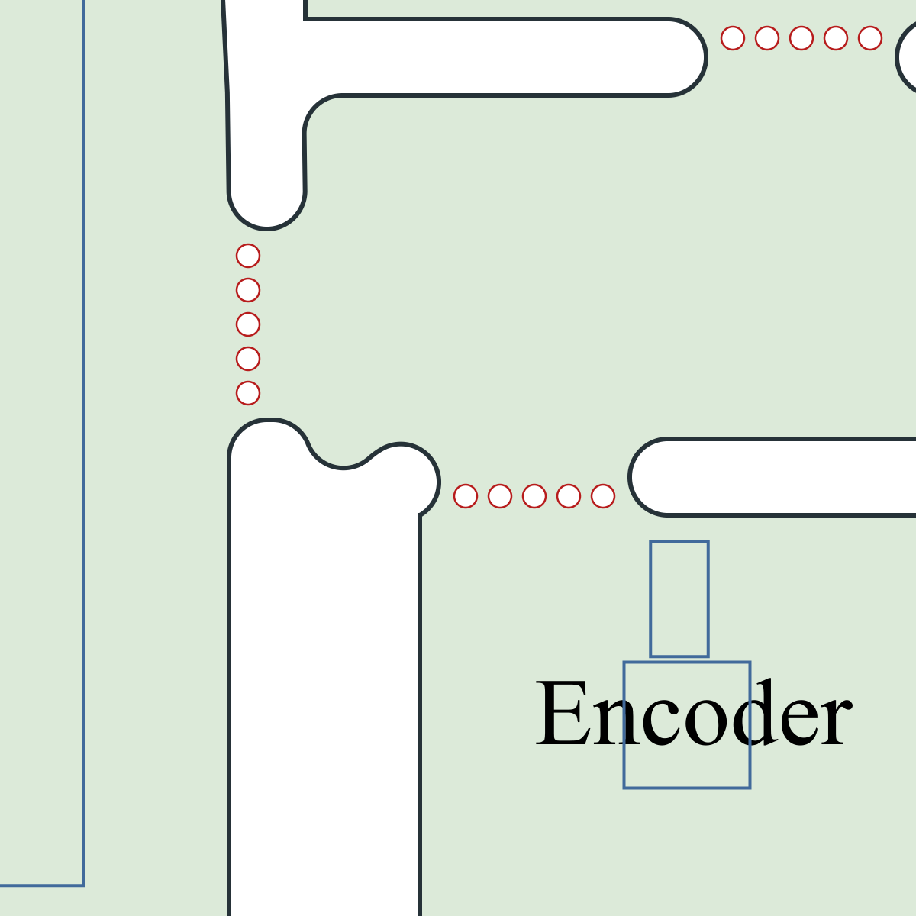
hardware/bench/copper-images/Panel-relocated-tabs.png
