sbarisic/MagMouse/hardware/bench/supplier-drafts/PLOOPY_COMPATIBILITY.md

# DRAFT — not sent

Subject: Exact PMW3360 sensor and lens identity for a private bench prototype

I plan to buy one replacement PMW3360 sensor/optic set from your consumer shop
for delivery to Croatia. This is a technical enquiry, not an order.

Could you confirm the exact sensor suffix and the included lens part number?
Our PCB is designed for PMW3360DM-T2QU and LM19-LSI. Please provide or identify
the applicable package/terminal drawing, lens locating features, sensor seating
height and lens-flange-to-surface stack. Is the included optic an unmodified
LM19-LSI or a Ploopy-specific part? Please also identify the supported firmware
initialisation/SROM source and soldering/cleaning requirements.

Prepared attachments: Main optical footprint/keepout view, Main placement view,
and the optical comparison in HARNESS_REVIEW.md. We need to check compatibility
before approving the board aperture; a PMW3360 product name alone is insufficient.

Use the reply contact supplied by the customer when they send this draft.
