sbarisic/MagMouse/hardware/bench/supplier-drafts/WURTH_FOLLOWUP.md

# SUPERSEDED — do not send

Rev-A now uses directly soldered AWG28 ribbon and through-hole arrays. No
FFC purchase or compatibility reply is required. The earlier enquiry remains
historical; no follow-up or cancellation message has been sent. The draft below
is retained only as an audit record and is not a manufacturing requirement.

Subject: Follow-up to 11 September 2026 Hirose-compatible 30-way FFC enquiry

This follows our existing enquiry submitted through your contact form on
11 September; please attach it to the original request rather than open a
duplicate. No order is being placed.

We need one or a few 150 mm, 30-way, 0.5 mm pitch, same-side-contact FFCs for
two Hirose FH12-30S-0.5SH(55) bottom-contact connectors. The recorded mating
requirements are conductor span 14.5 +/-0.05 mm, width 15.5 +/-0.07 mm, end
thickness 0.30 +/-0.05 mm, exposed contacts >=3.5 mm and stiffener >=0.188 mm.

Please identify an exact compatible MPN with toleranced end/stiffener drawing,
insertion requirements, static bend radius, MOQ and private-consumer purchasing
route shipping to Croatia 43000. A catalogue cable previously reviewed did not
satisfy every dimension; nominal pitch and conductor count are not sufficient.

Prepared attachments: HARNESS_REVIEW.md, Main-J8/Wheel-J9 pin views and the
30-row FFC portion of harness-pin-map.csv. Electrical mapping is J8.N to
J9.(31-N). Use the reply contact on the original request.
