sbarisic/MagMouse/hardware/bench/package/paste-shape-measurements.csv

Board | Reference | Pad | Primitive_count | Area_mm2 | Perimeter_mm | Thickness_mm | Polygon_wkt | Volume_mm3 | Area_ratio | X_mm | Y_mm | Rotation_deg | Status
Main | D5 | 1 | 1 | 0.3025 | 2.2 | 0.1 | POLYGON ((41.5 26.95, 42.05 26.95, 42.05 27.5, 41.5 27.5, 41.5 26.95)) | 0.03025 | 1.375 | 41.775 | 27.22500000000001 | 0.0 | Geometric release screen passes
Main | D5 | 2 | 1 | 0.3025 | 2.2 | 0.1 | POLYGON ((42.45 26.95, 43 26.95, 43 27.5, 42.45 27.5, 42.45 26.95)) | 0.03025 | 1.375 | 42.725 | 27.22500000000001 | 0.0 | Geometric release screen passes
Main | D5 | 3 | 1 | 0.3025 | 2.2 | 0.1 | POLYGON ((42.45 26, 43 26, 43 26.55, 42.45 26.55, 42.45 26)) | 0.03025 | 1.375 | 42.725 | 26.274999999999995 | 0.0 | Geometric release screen passes
Main | D5 | 4 | 1 | 0.3025 | 2.2 | 0.1 | POLYGON ((41.5 26, 42.05 26, 42.05 26.55, 41.5 26.55, 41.5 26)) | 0.03025 | 1.375 | 41.775 | 26.274999999999995 | 0.0 | Geometric release screen passes
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
Main | U14 | 3 | 1 | 0.351872 | 2.598028 | 0.1 | POLYGON ((22.9 46.0625, 22.901525 46.046233, 22.91014 46.021614, 22.925628 46.000628, 22.946614 45.98514, 22.971233 45.976525, 22.9875 45.975, 23.8375 45.975, 23.853767 45.976525, 23.878386 45.98514, 23.899372 46.000628, 23.91486 46.021614, 23.923475 46.046233, 23.925 46.0625, 23.925 46.2375, 23.923475 46.253767, 23.91486 46.278386, 23.899372 46.299372, 23.878386 46.31486, 23.853767 46.323475, 23.8375 46.325, 22.9875 46.325, 22.971233 46.323475, 22.946614 46.31486, 22.925628 46.299372, 22.91014 46.278386, 22.901525 46.253767, 22.9 46.2375, 22.9 46.0625)) | 0.035187 | 1.3544 | 23.4125 | 46.150000000000006 | 0.0 | Geometric release screen passes
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
