sbarisic/MagMouse/mechanical/bench/generated/ribbon_clamp_cap.step

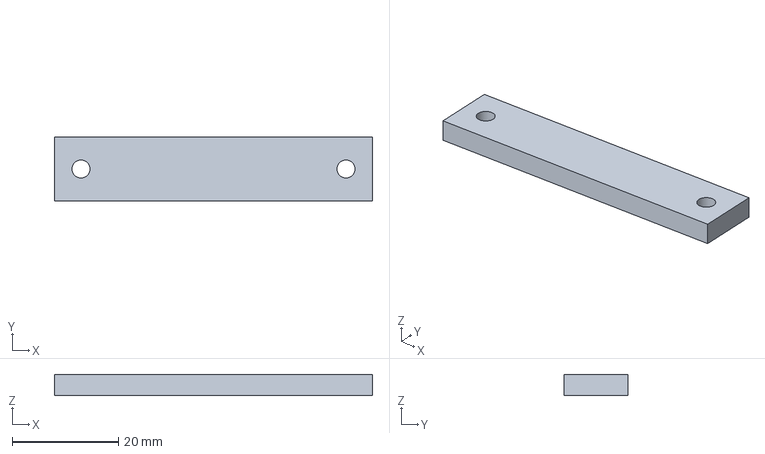
[picture p76: CAD file, 2026-09-13]
mechanical/bench/generated/ribbon_clamp_cap.step
60.0 x 12.0 x 4.00 mm
