sbarisic/MagMouse/hardware/bench/package/fixture/pair_clamp_base.step

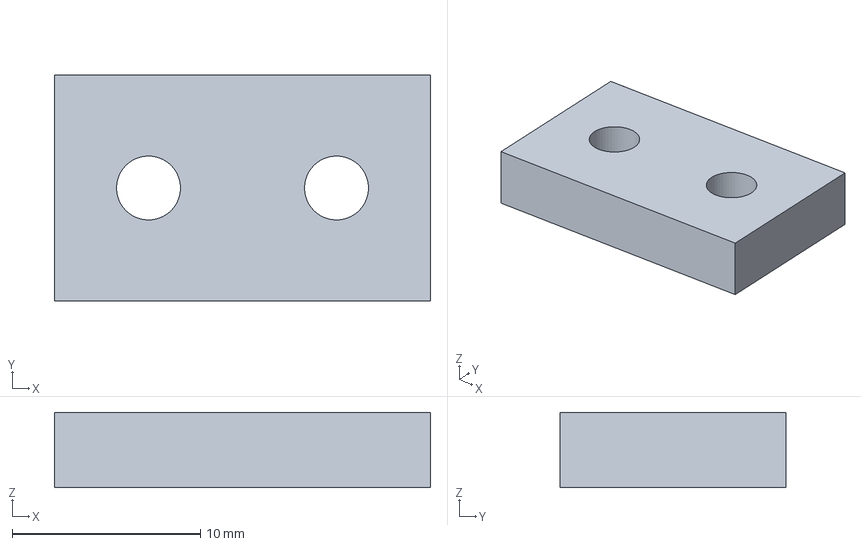
[picture p77: CAD file, 2026-09-13]
hardware/bench/package/fixture/pair_clamp_base.step
20.0 x 12.0 x 4.00 mm
