sbarisic/MagMouse/hardware/bench/package/fixture/button_stop.step

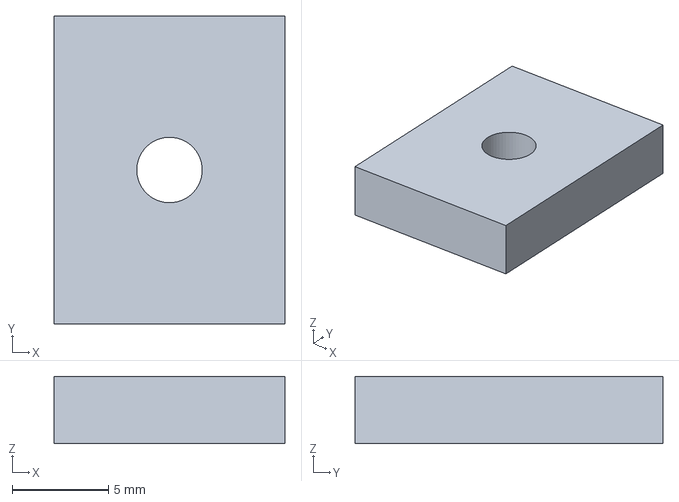
[picture p78: CAD file, 2026-09-13]
hardware/bench/package/fixture/button_stop.step
12.0 x 16.0 x 3.50 mm
