sbarisic/MagMouse/mechanical/bench/generated/base_0_0.step

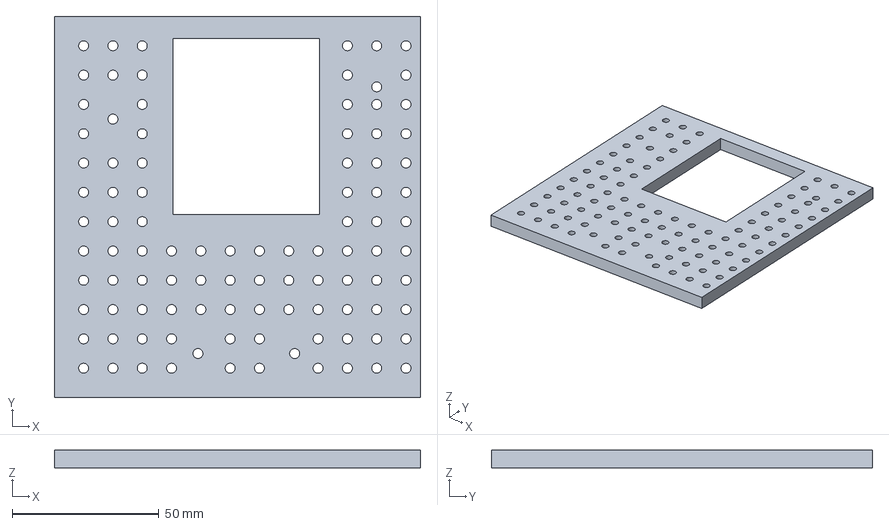
[picture p79: CAD file, 2026-09-13]
mechanical/bench/generated/base_0_0.step
125.0 x 130.0 x 6.00 mm
