sbarisic/MagMouse/hardware/simulation/brake/results/waveforms.png

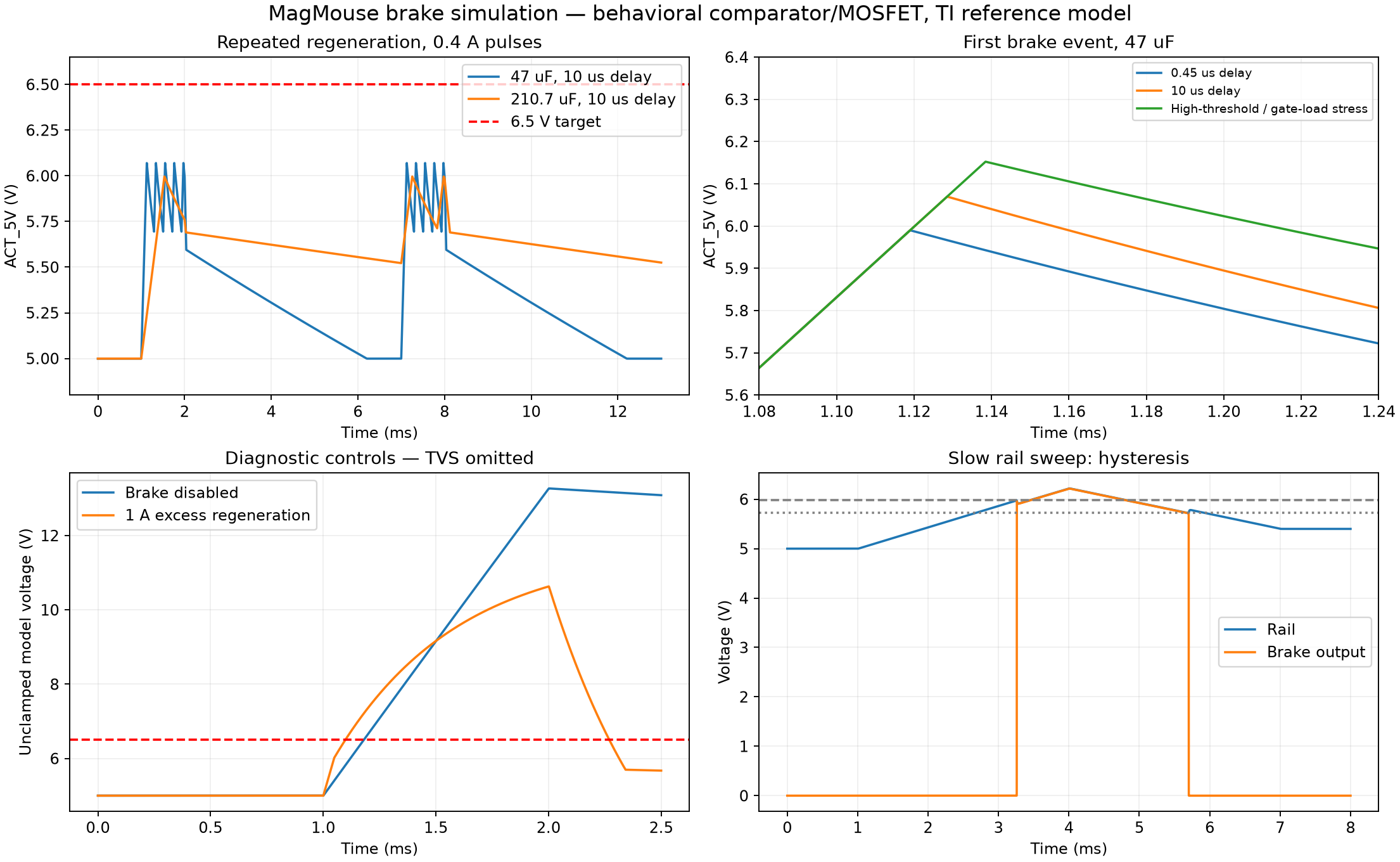
hardware/simulation/brake/results/waveforms.png
